wenzel-lab/flow-microscopy-platform/parts/optics/8.7-20mm-circular-lens.md

# 8.7° 20mm Circular Beam Optics

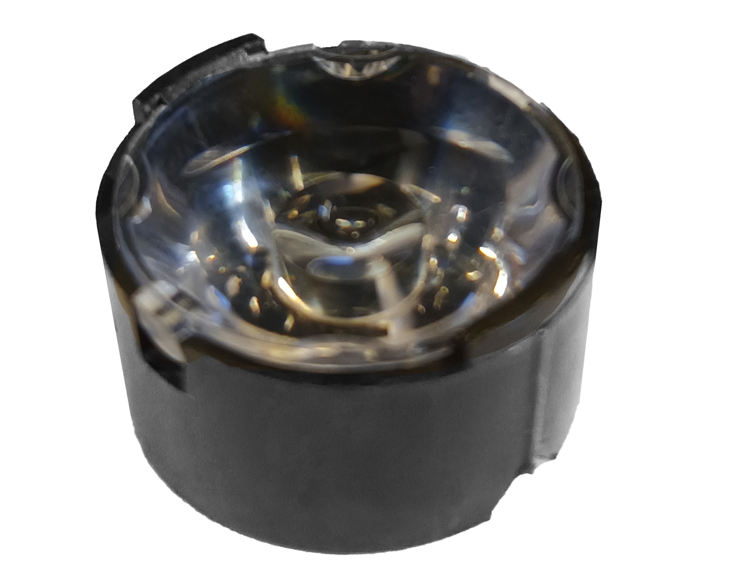
[picture p37: images/LED3.jpg]


_Suppliers:_ 

* [Luxeonstar / Lens](https://www.luxeonstar.com/carclo-8.7-degree-20mm-optic)

* [Luxeonstar / Holder](https://www.luxeonstar.com/carclo-20mm-round-optic-holder-black)
