wenzel-lab/flow-microscopy-platform/resin-legs.md

# Resin filled legs

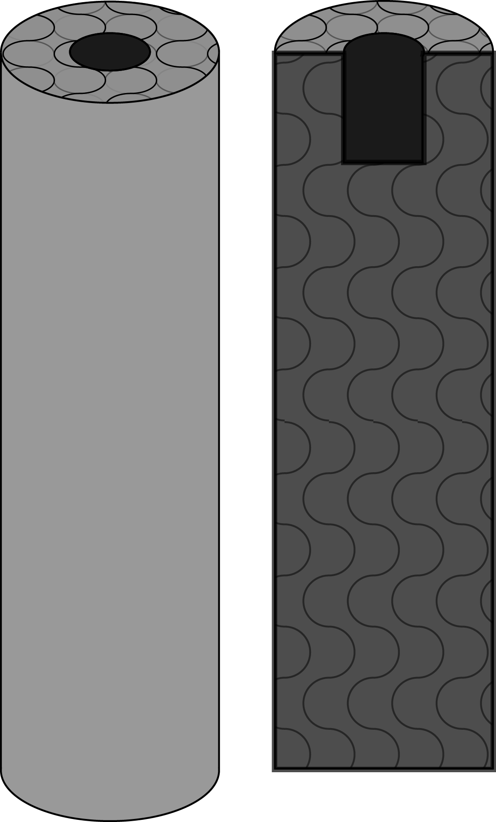
[picture p52: images/patas.jpg]


###What are they?

They are...

###How do we make them?

First...

>i **Please Note:** 
>i This site is under construction.
