wenzel-lab/flow-microscopy-platform/images/2-levels.jpg

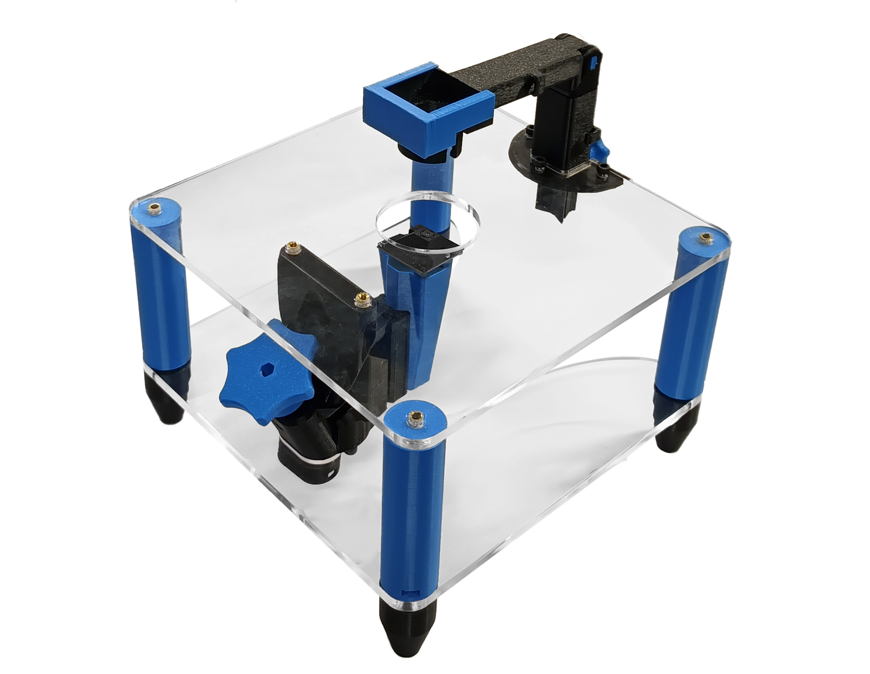
images/2-levels.jpg
