wenzel-lab/flow-microscopy-platform/images/2pin-du-pont-connector.png

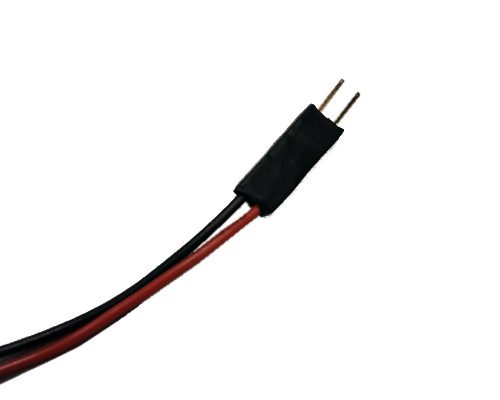
images/2pin-du-pont-connector.png
