wenzel-lab/flow-microscopy-platform/images/3-level-station.jpg

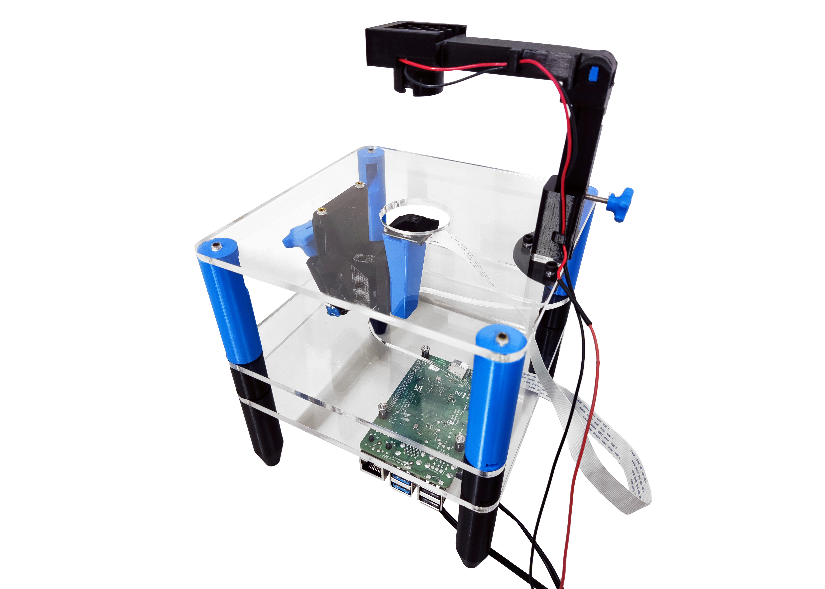
images/3-level-station.jpg
