wenzel-lab/flow-microscopy-platform/images/arm-slider.png

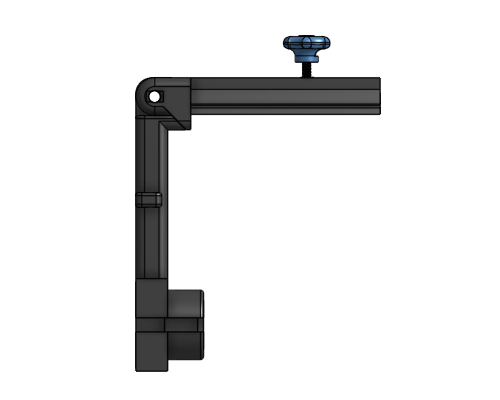
images/arm-slider.png
