wenzel-lab/flow-microscopy-platform/images/arm-slider_1.png

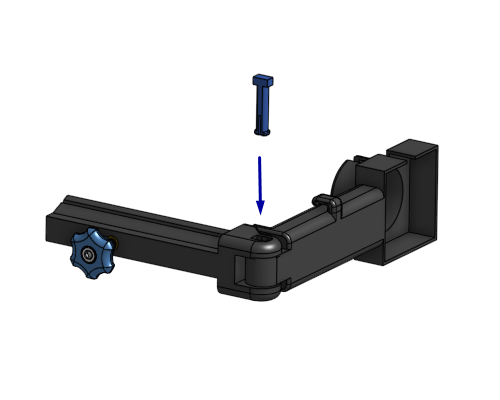
images/arm-slider_1.png
