wenzel-lab/flow-microscopy-platform/images/arm-slider_2.png

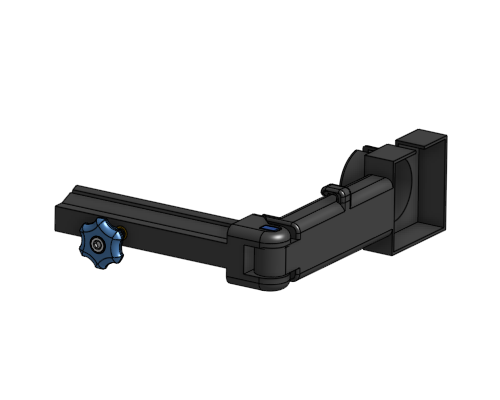
images/arm-slider_2.png
