wenzel-lab/flow-microscopy-platform/images/BrimRemoval.png

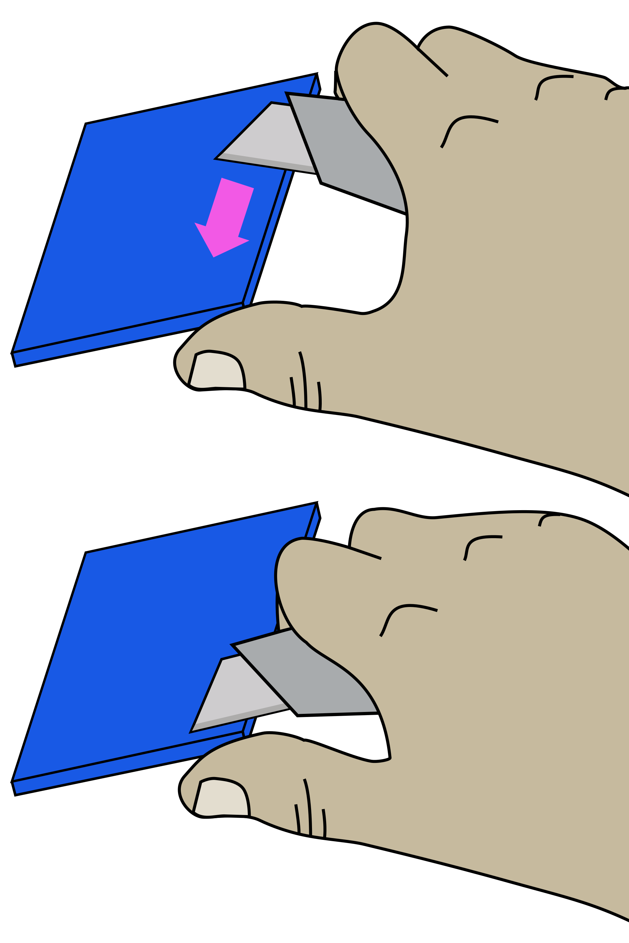
images/BrimRemoval.png
