wenzel-lab/flow-microscopy-platform/images/cable-clip.jpg

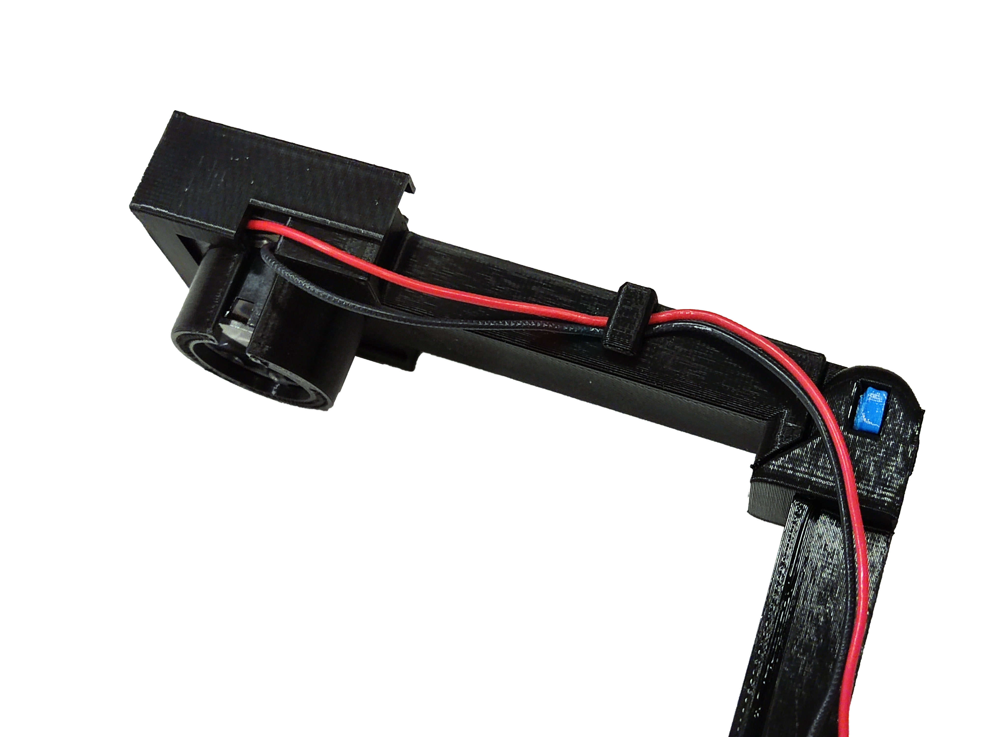
images/cable-clip.jpg
