wenzel-lab/flow-microscopy-platform/images/cable-clip_1.jpg

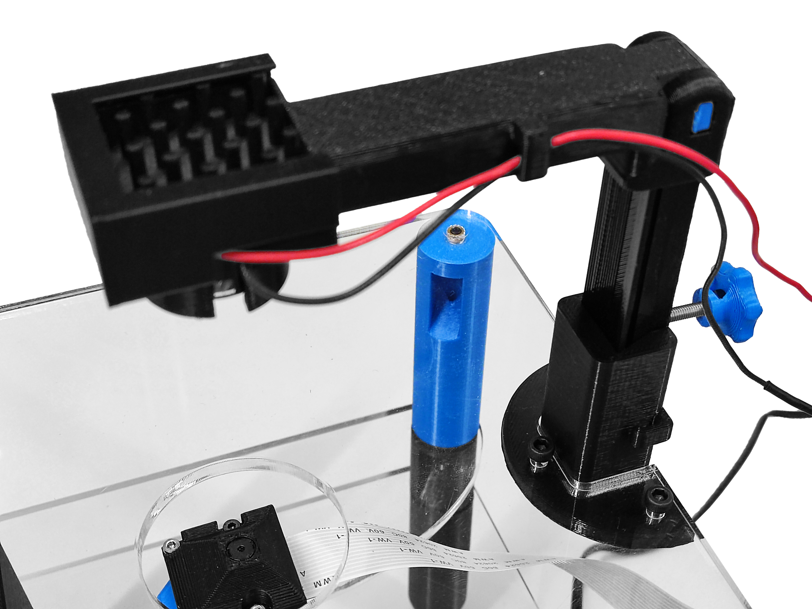
images/cable-clip_1.jpg
