wenzel-lab/flow-microscopy-platform/images/cable-clip_2.jpg

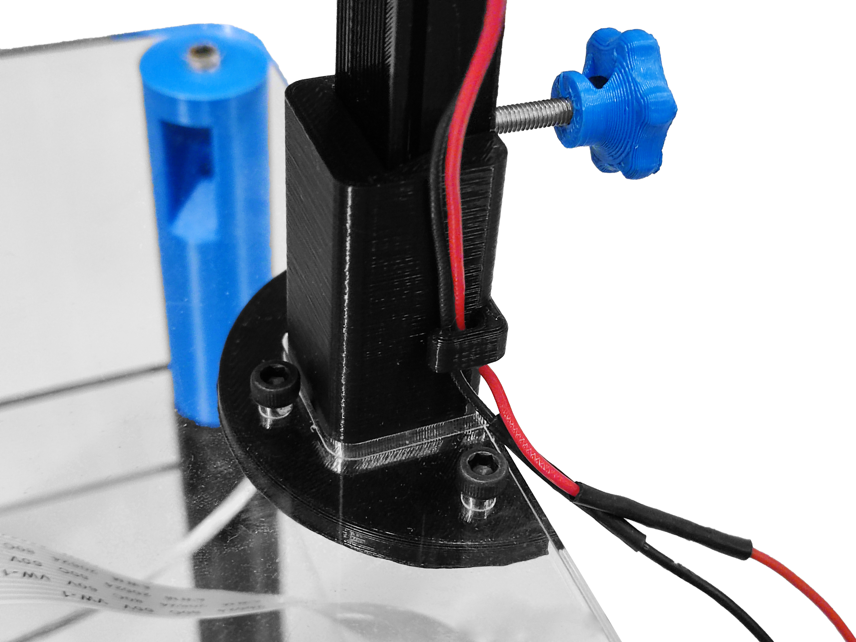
images/cable-clip_2.jpg
