wenzel-lab/flow-microscopy-platform/images/cable-clip_3.jpg

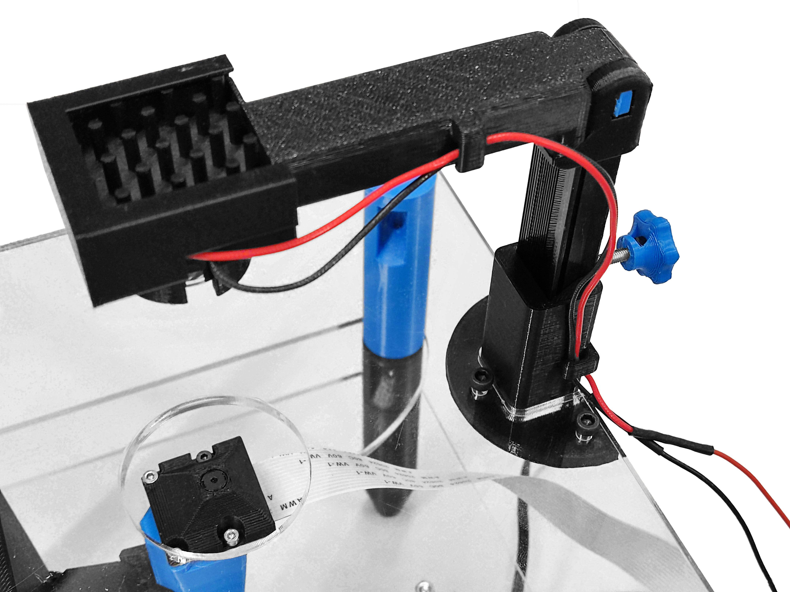
images/cable-clip_3.jpg
