wenzel-lab/flow-microscopy-platform/images/cap.jpg

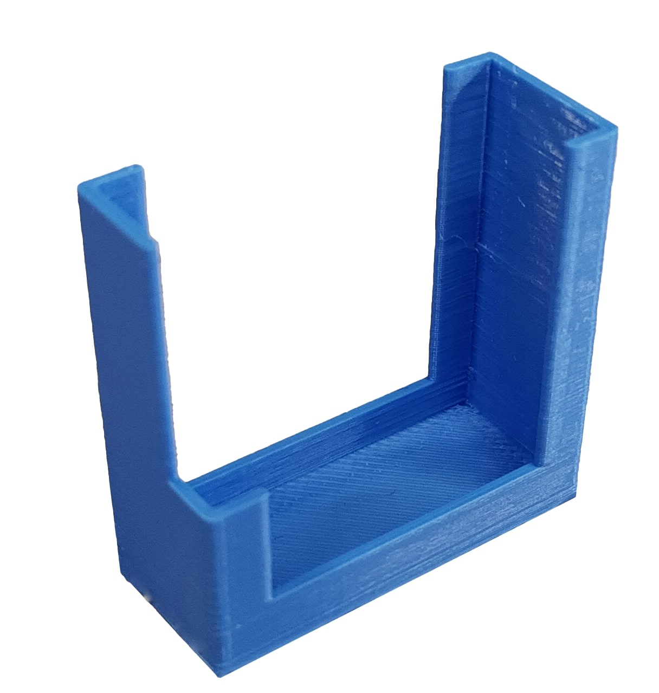
images/cap.jpg
