wenzel-lab/flow-microscopy-platform/images/DuPont-2PIN-Connector.jpg

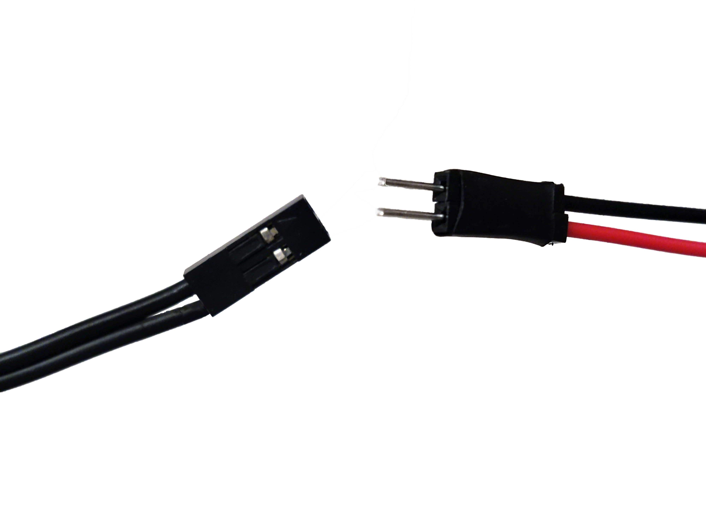
images/DuPont-2PIN-Connector.jpg
