wenzel-lab/flow-microscopy-platform/images/feet-M-attached.jpg

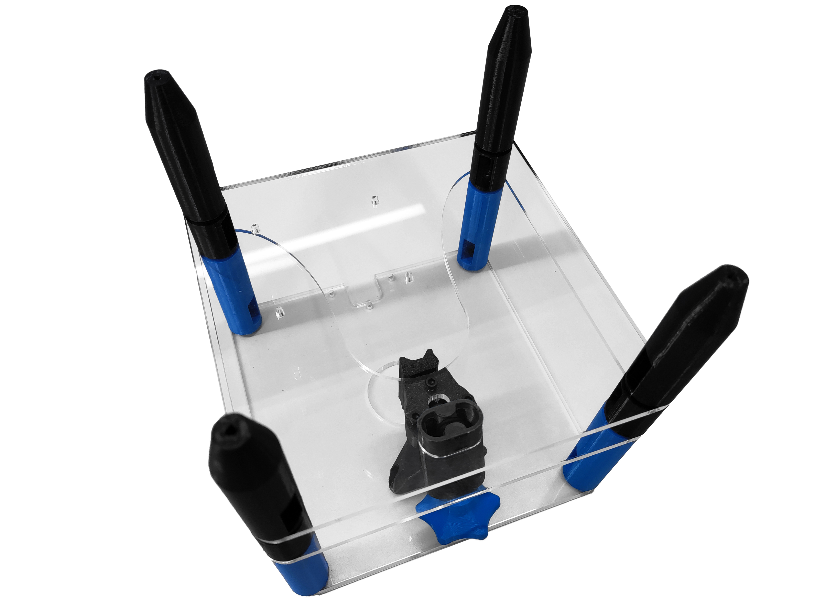
images/feet-M-attached.jpg
