wenzel-lab/flow-microscopy-platform/images/feet-M-attached_1.jpg

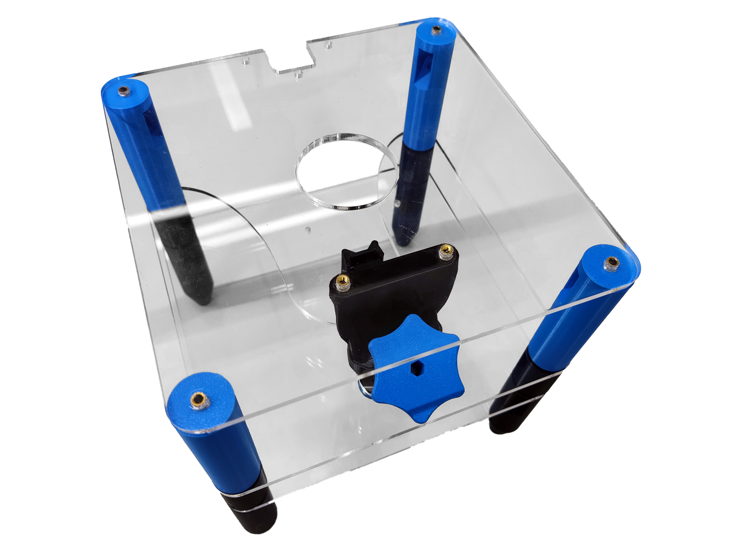
images/feet-M-attached_1.jpg
