wenzel-lab/flow-microscopy-platform/images/Female-crimp-pin.jpg

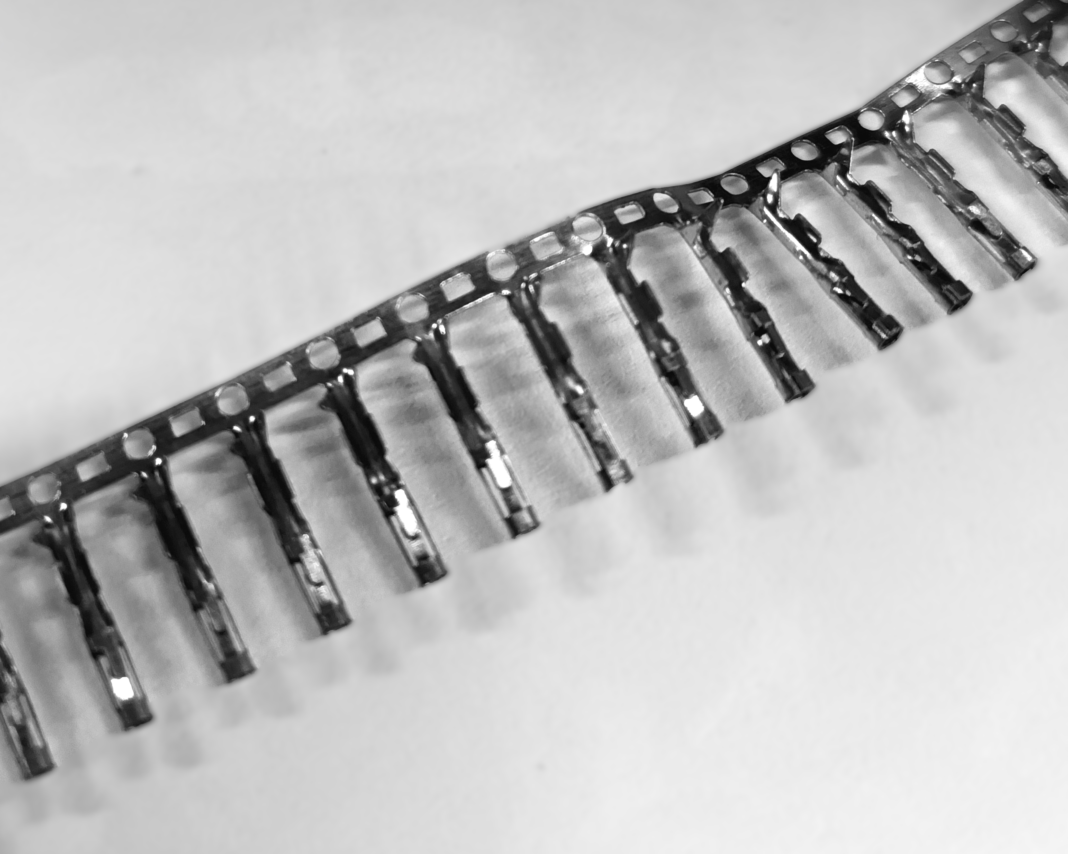
images/Female-crimp-pin.jpg
