wenzel-lab/flow-microscopy-platform/images/flow-platform.jpg

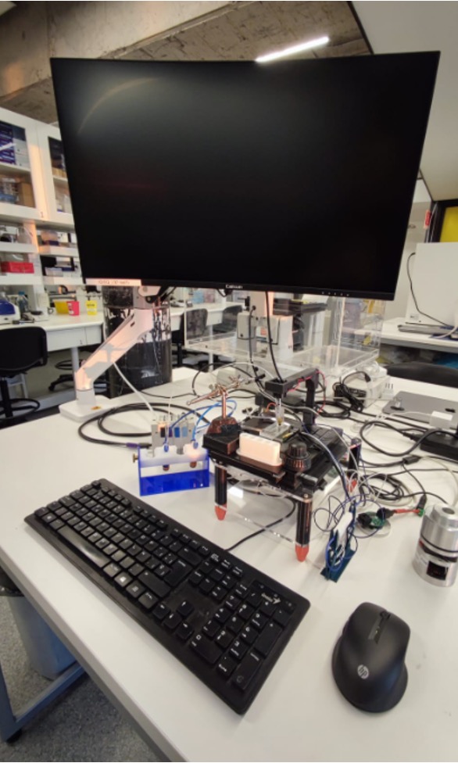
images/flow-platform.jpg
