wenzel-lab/flow-microscopy-platform/images/foot-M-attached.jpg

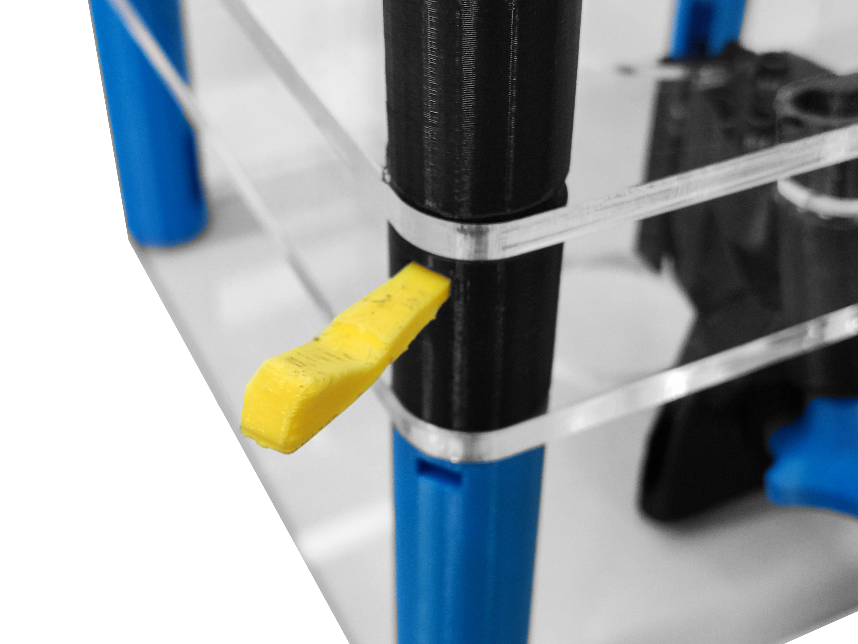
images/foot-M-attached.jpg
