wenzel-lab/flow-microscopy-platform/images/foot-M-attached_1.jpg

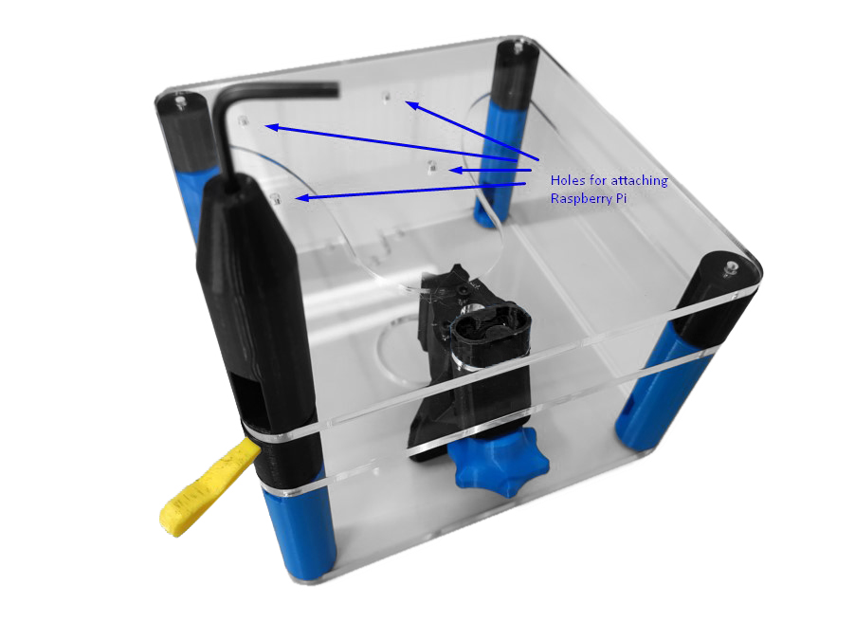
images/foot-M-attached_1.jpg
