wenzel-lab/flow-microscopy-platform/images/foot-M-attached_2.jpg

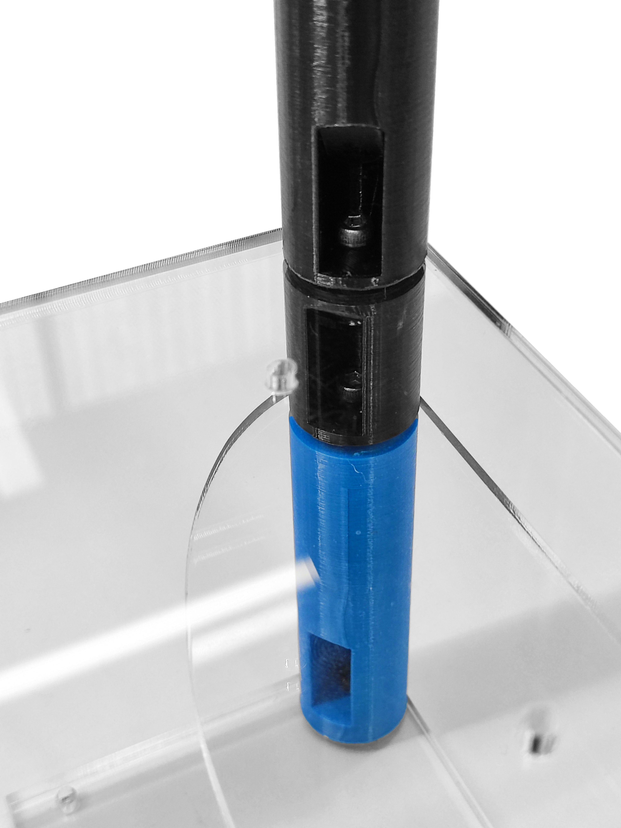
images/foot-M-attached_2.jpg
