wenzel-lab/flow-microscopy-platform/images/foot-M-attached_3.jpg

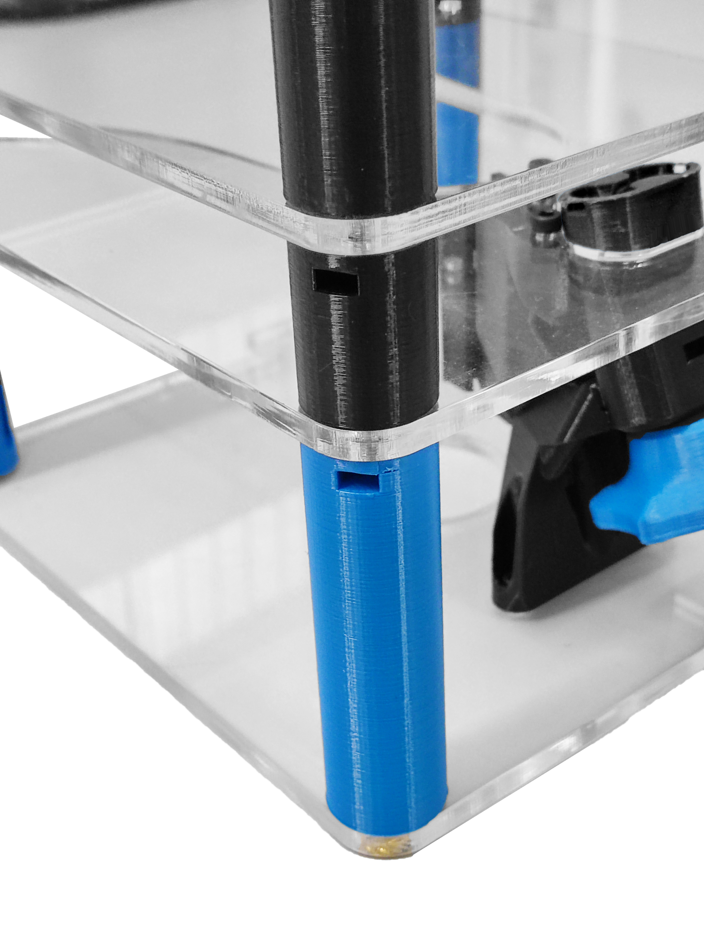
images/foot-M-attached_3.jpg
