wenzel-lab/flow-microscopy-platform/images/foot-M.jpg

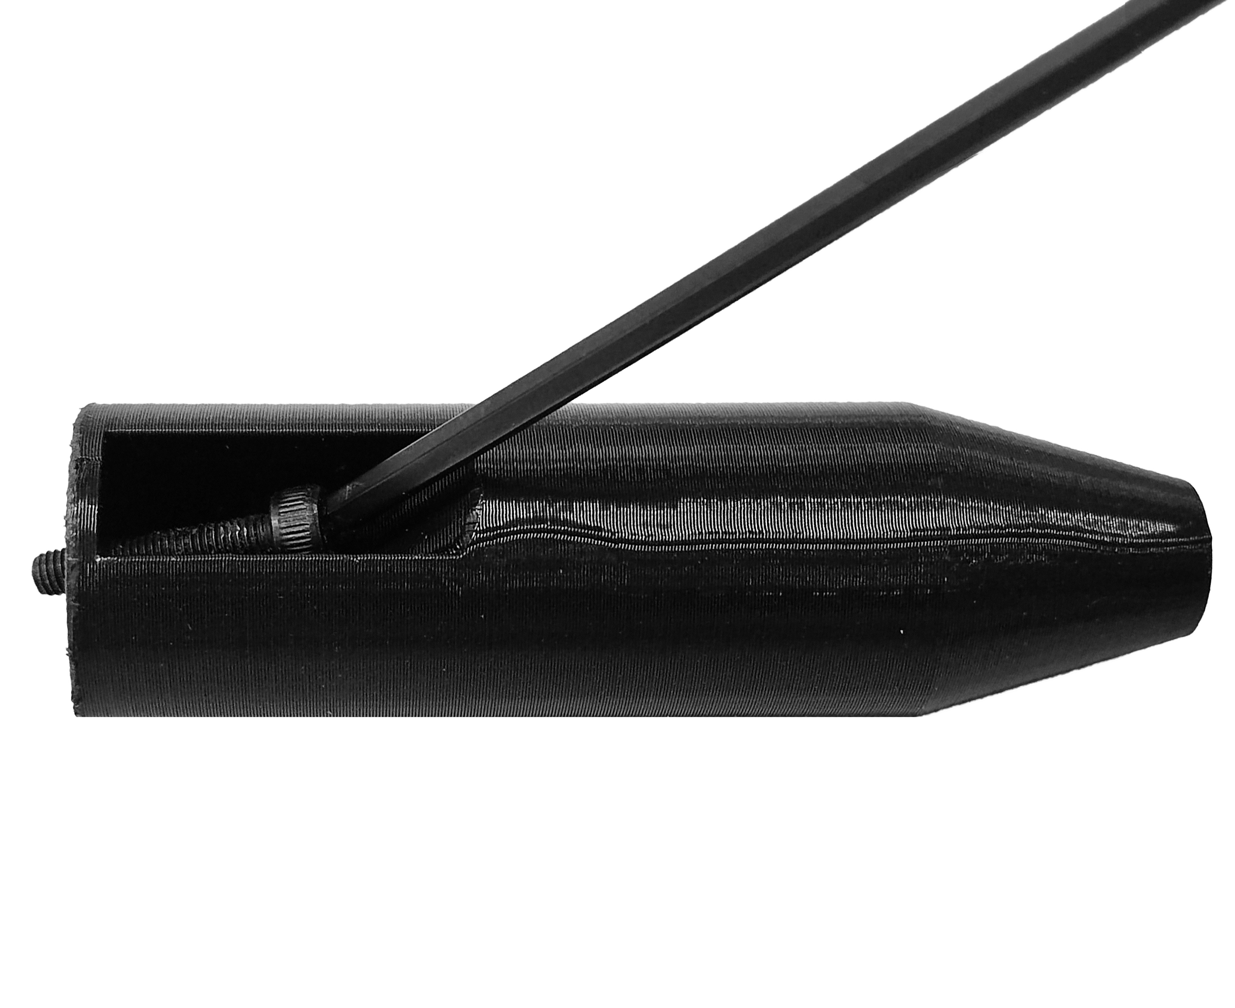
images/foot-M.jpg
