wenzel-lab/flow-microscopy-platform/images/heat-insert_top-plate.png

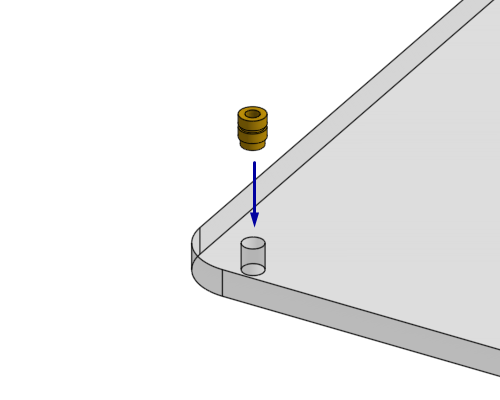
images/heat-insert_top-plate.png
