wenzel-lab/flow-microscopy-platform/images/heat-insert_top-plate_1.png

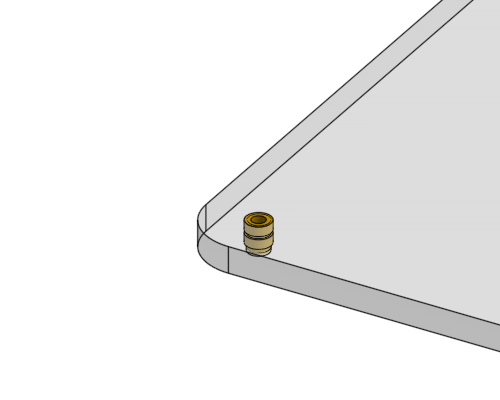
images/heat-insert_top-plate_1.png
