wenzel-lab/flow-microscopy-platform/images/heat-insert_top-plate_2.png

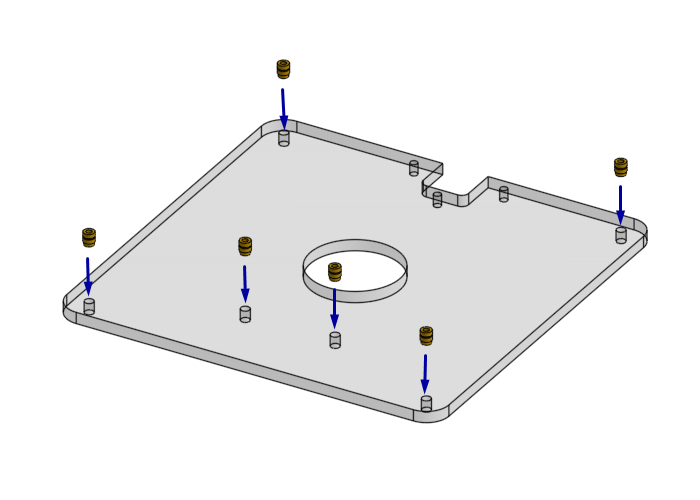
images/heat-insert_top-plate_2.png
