wenzel-lab/flow-microscopy-platform/images/heat-insert_top-plate_3.png

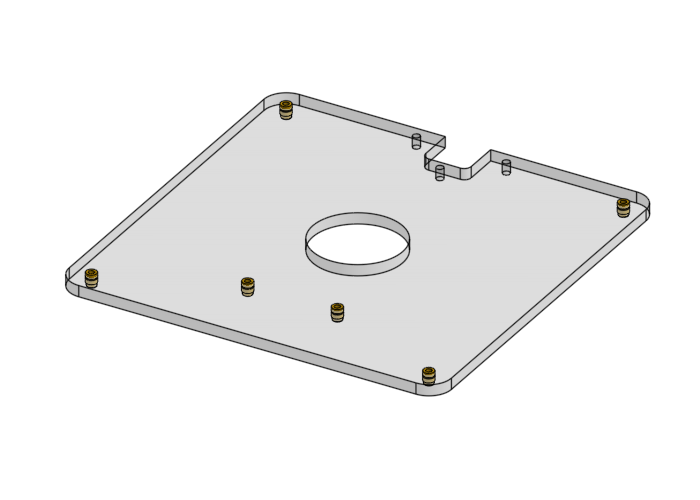
images/heat-insert_top-plate_3.png
