wenzel-lab/flow-microscopy-platform/images/iii.jpg

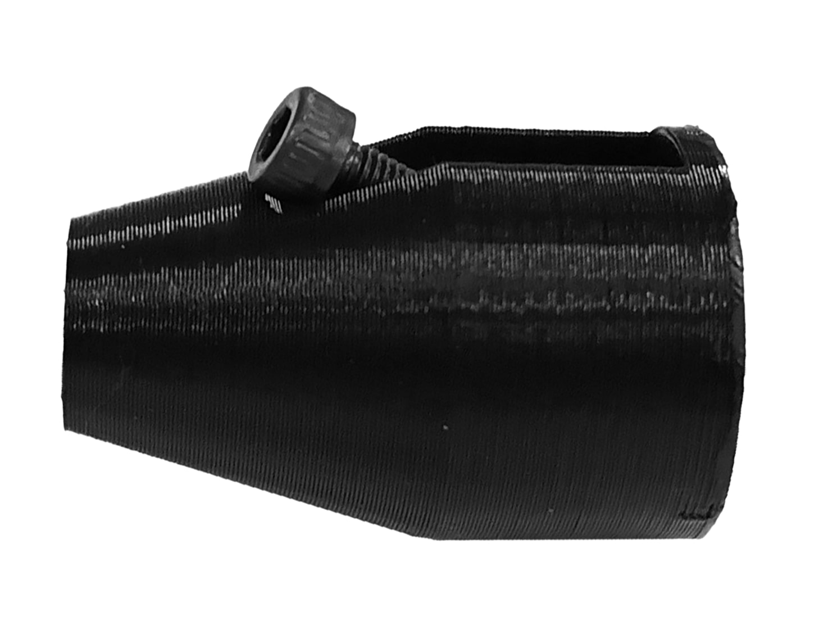
images/iii.jpg
