wenzel-lab/flow-microscopy-platform/images/LED1.jpg

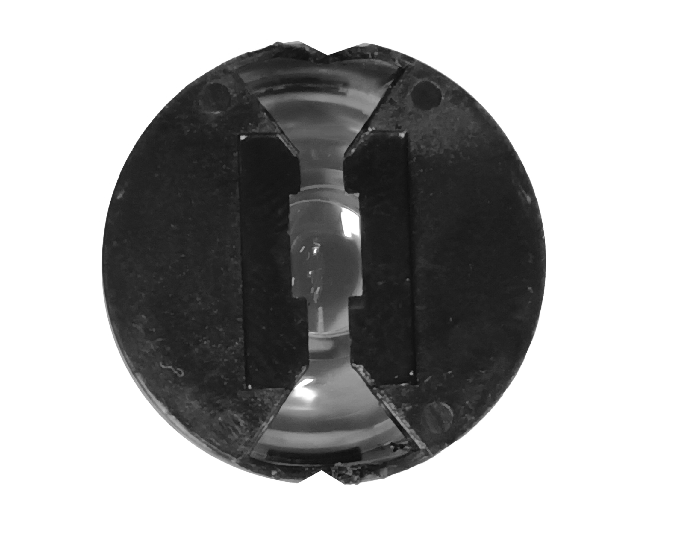
images/LED1.jpg
