wenzel-lab/flow-microscopy-platform/images/LED4.jpg

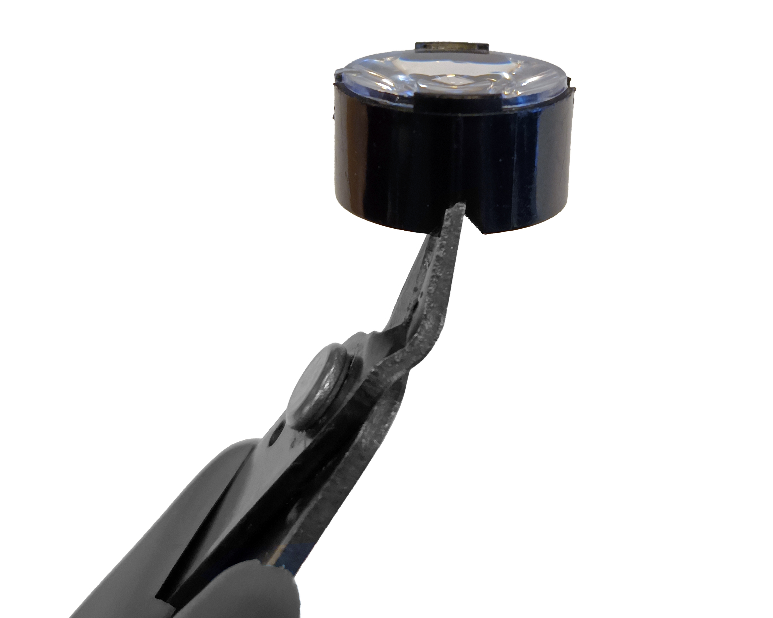
images/LED4.jpg
