wenzel-lab/flow-microscopy-platform/images/led-lens-sink.png

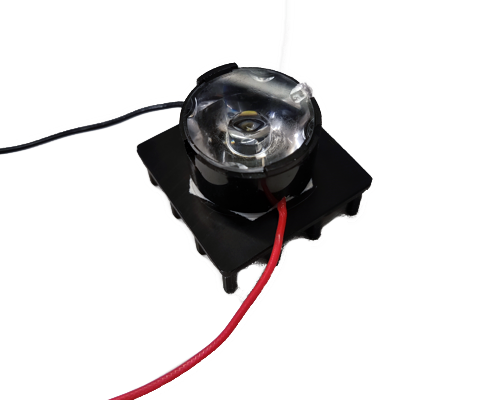
images/led-lens-sink.png
