wenzel-lab/flow-microscopy-platform/images/LED.jpg

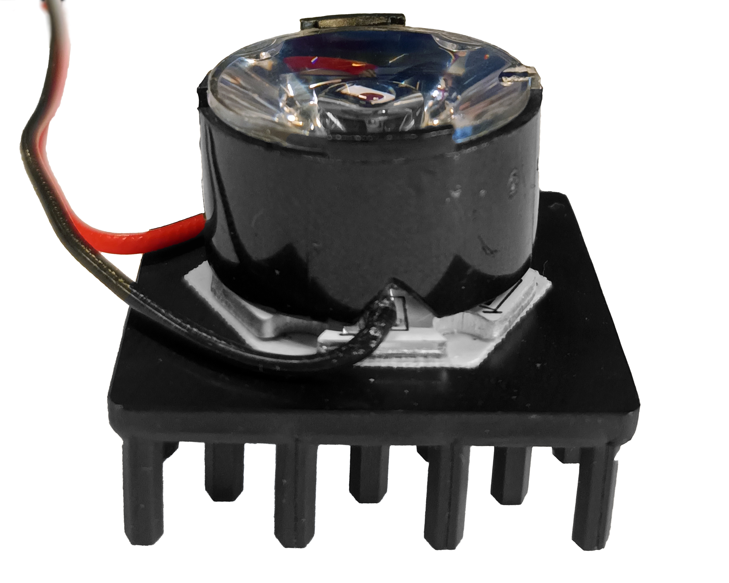
images/LED.jpg
