wenzel-lab/flow-microscopy-platform/images/lens-holder-1.png

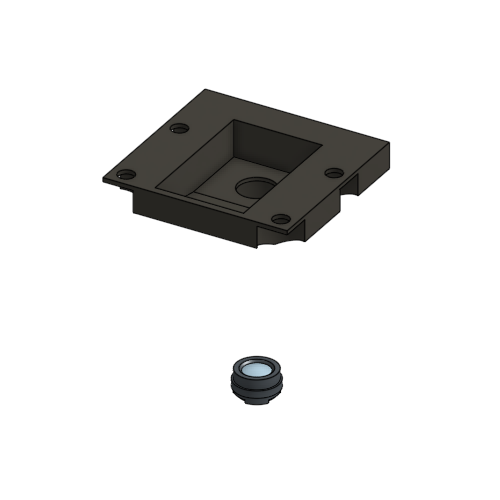
images/lens-holder-1.png
