wenzel-lab/flow-microscopy-platform/images/lens-holder-2.png

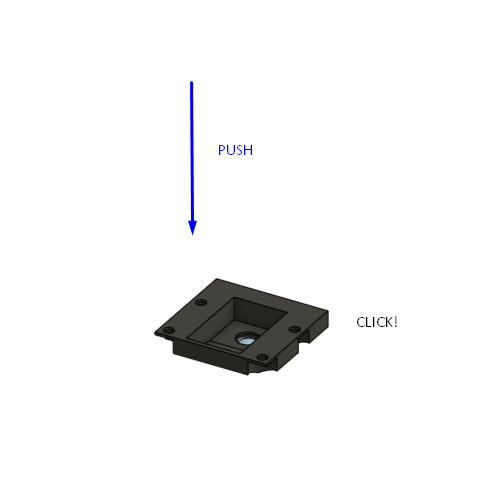
images/lens-holder-2.png
