wenzel-lab/flow-microscopy-platform/images/lens-holder-3.png

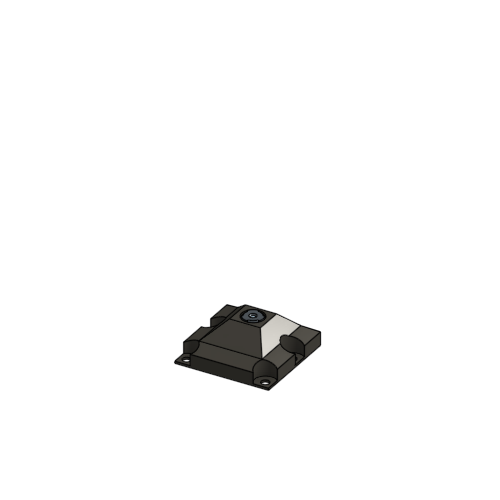
images/lens-holder-3.png
