wenzel-lab/flow-microscopy-platform/images/LH-Hinsert.jpg

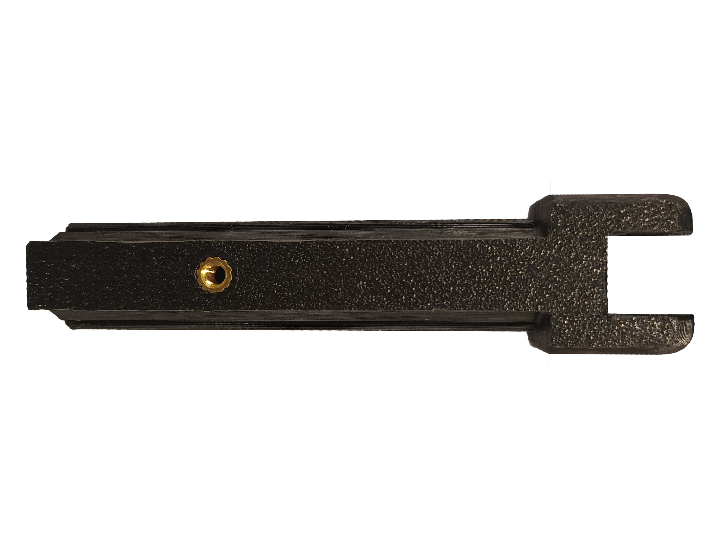
images/LH-Hinsert.jpg
