wenzel-lab/flow-microscopy-platform/images/LH-knob.jpg

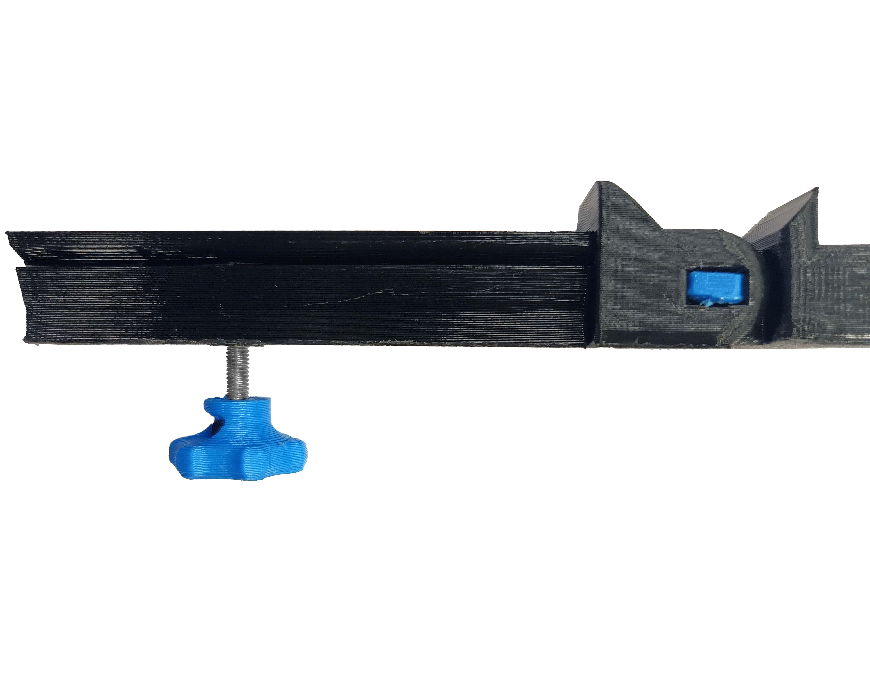
images/LH-knob.jpg
