wenzel-lab/flow-microscopy-platform/images/LH-pin.jpg

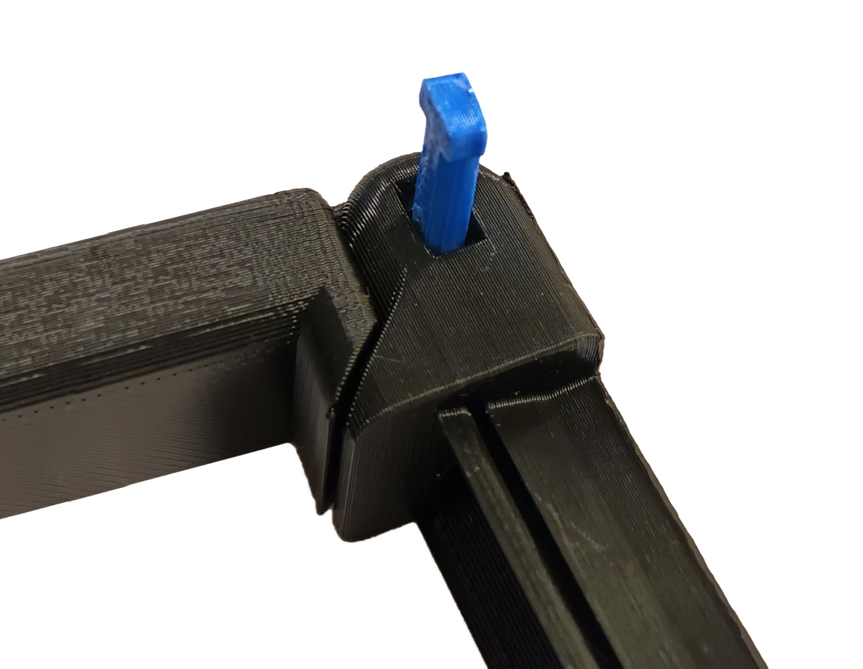
images/LH-pin.jpg
