wenzel-lab/flow-microscopy-platform/images/middle_plate_to_focus.jpg

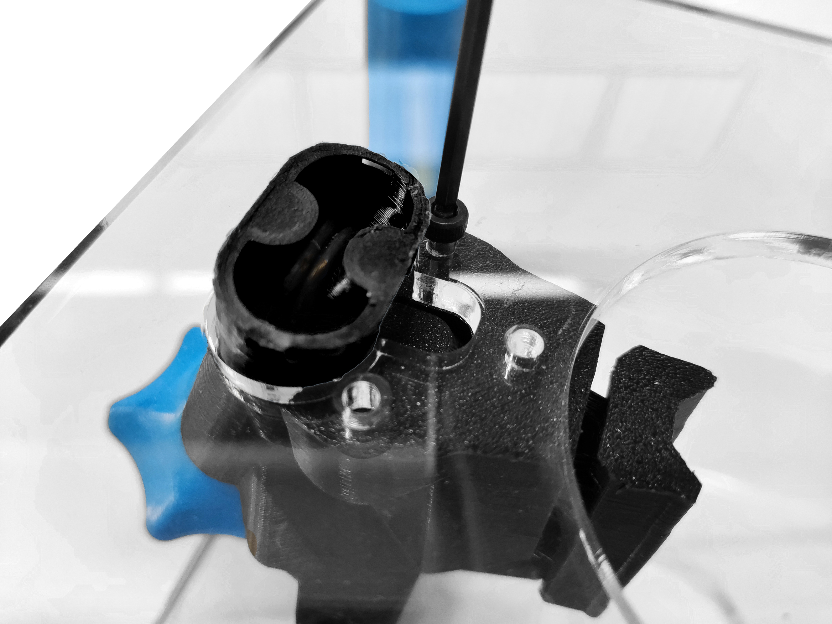
images/middle_plate_to_focus.jpg
