wenzel-lab/flow-microscopy-platform/images/mount-screw-1.png

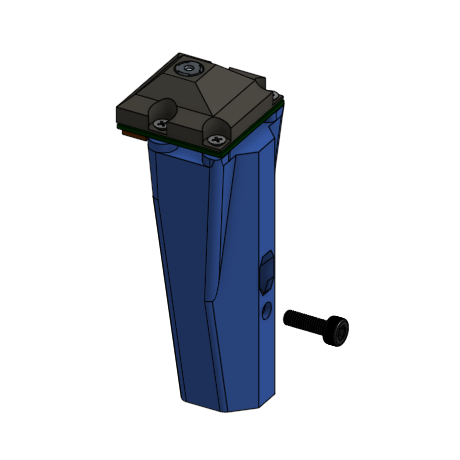
images/mount-screw-1.png
