wenzel-lab/flow-microscopy-platform/images/mount-screw.png

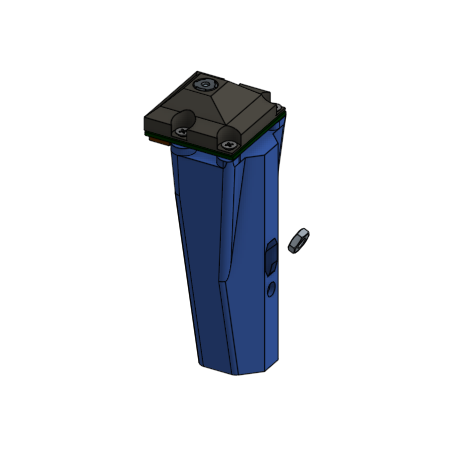
images/mount-screw.png
