wenzel-lab/flow-microscopy-platform/images/mount_base.png

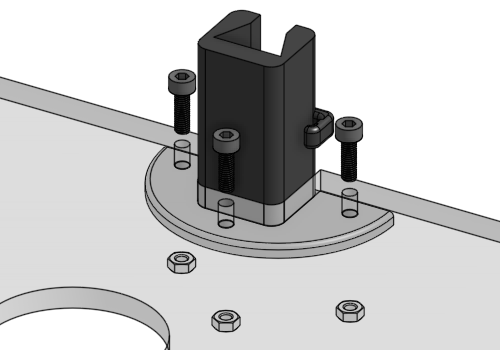
images/mount_base.png
