wenzel-lab/flow-microscopy-platform/images/mount_base_1.png

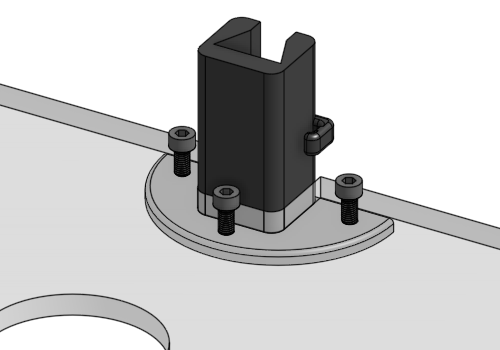
images/mount_base_1.png
