wenzel-lab/flow-microscopy-platform/images/mount_base_2.png

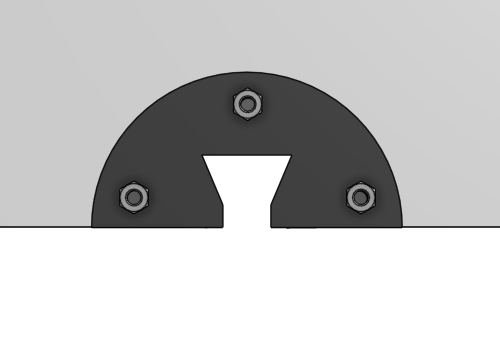
images/mount_base_2.png
