wenzel-lab/flow-microscopy-platform/images/mount_boards_3.jpg

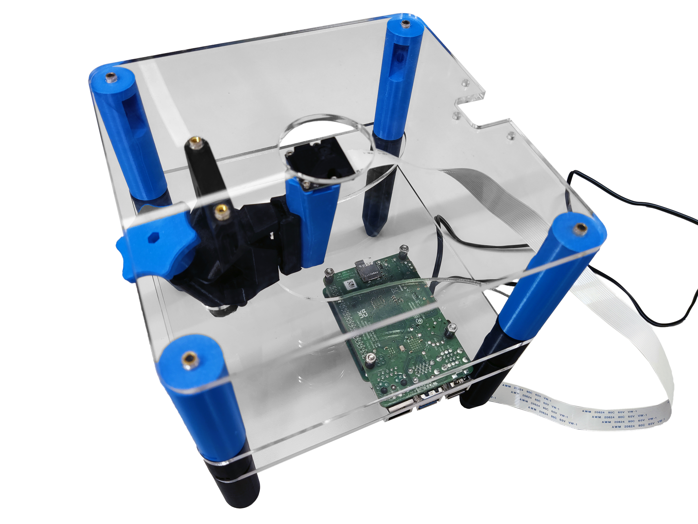
images/mount_boards_3.jpg
