wenzel-lab/flow-microscopy-platform/images/mount_optics.jpg

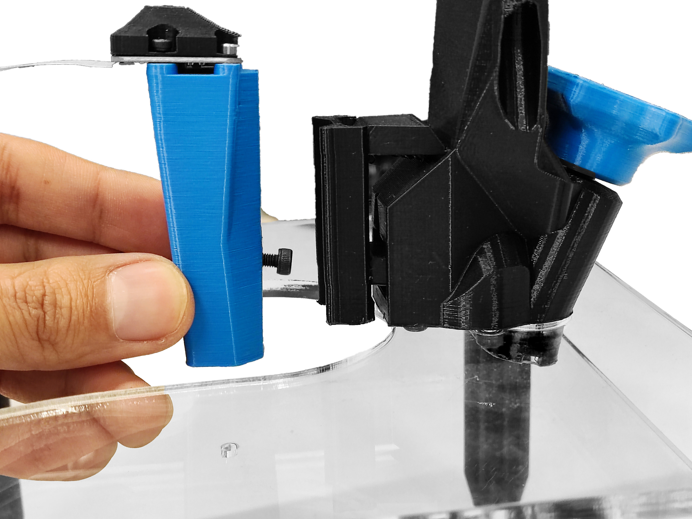
images/mount_optics.jpg
