wenzel-lab/flow-microscopy-platform/images/mount_optics_1.jpg

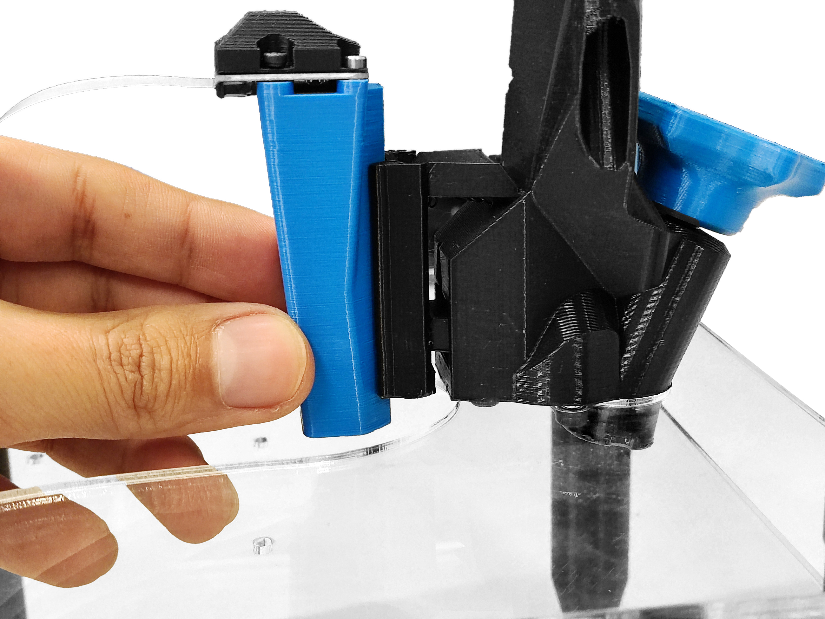
images/mount_optics_1.jpg
