wenzel-lab/flow-microscopy-platform/images/mount_spacers.jpg

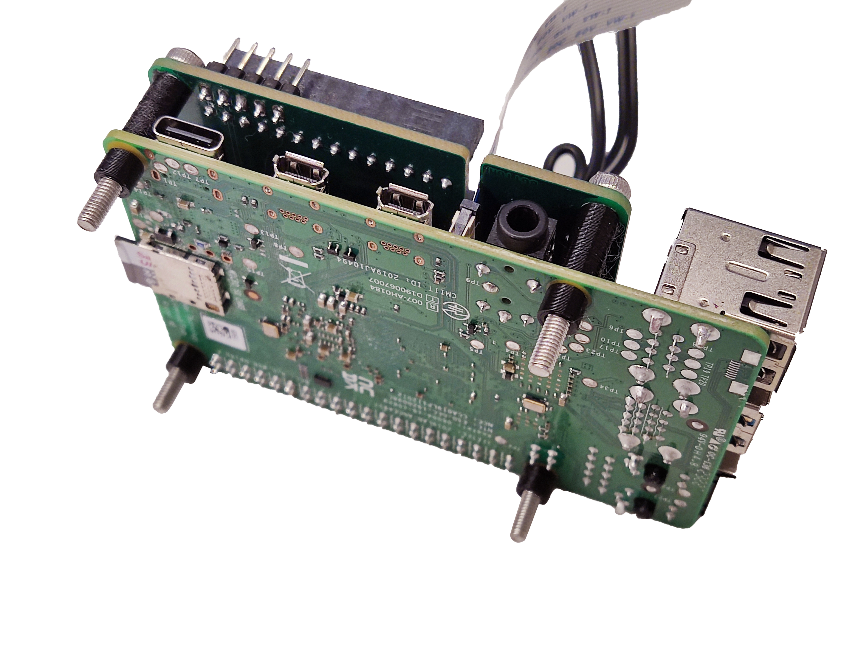
images/mount_spacers.jpg
