wenzel-lab/flow-microscopy-platform/images/nutpushers.jpg

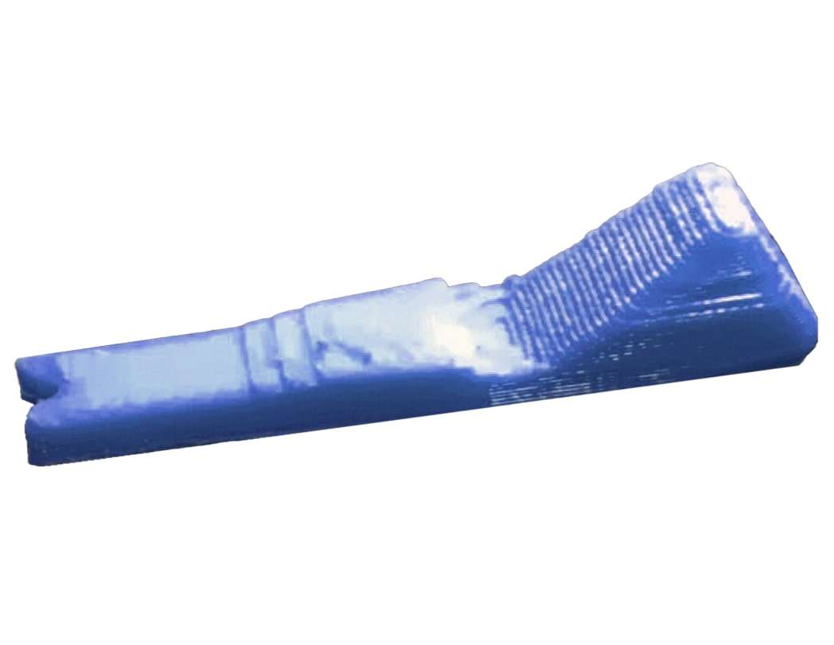
images/nutpushers.jpg
