wenzel-lab/flow-microscopy-platform/images/partelight.jpg

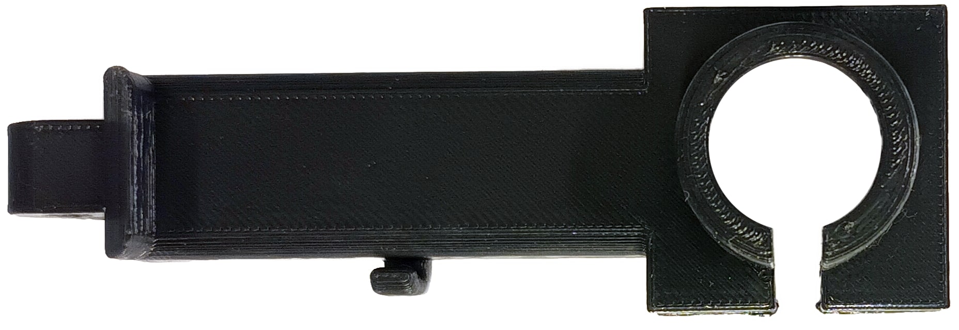
images/partelight.jpg
