wenzel-lab/flow-microscopy-platform/images/partelighthold.jpg

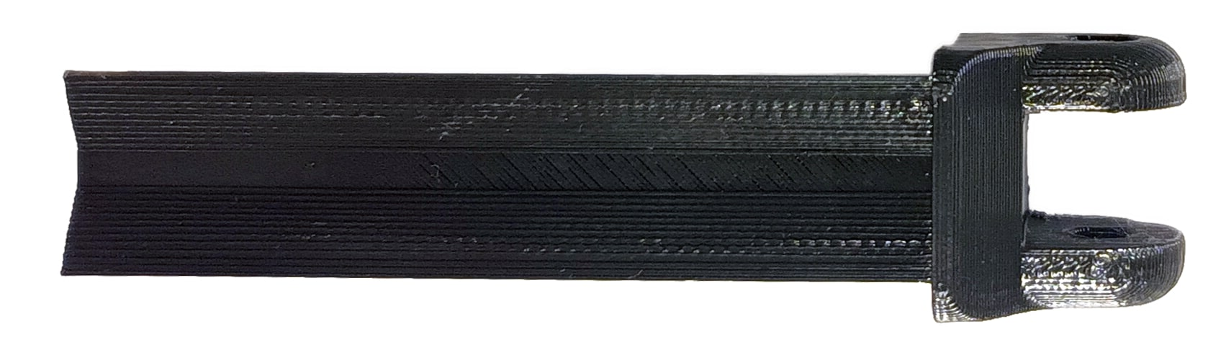
images/partelighthold.jpg
