wenzel-lab/flow-microscopy-platform/images/partelightholder.jpg

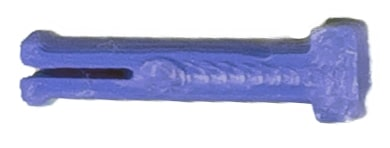
images/partelightholder.jpg
