wenzel-lab/flow-microscopy-platform/images/Pi-Hat_StrobeModule.jpg

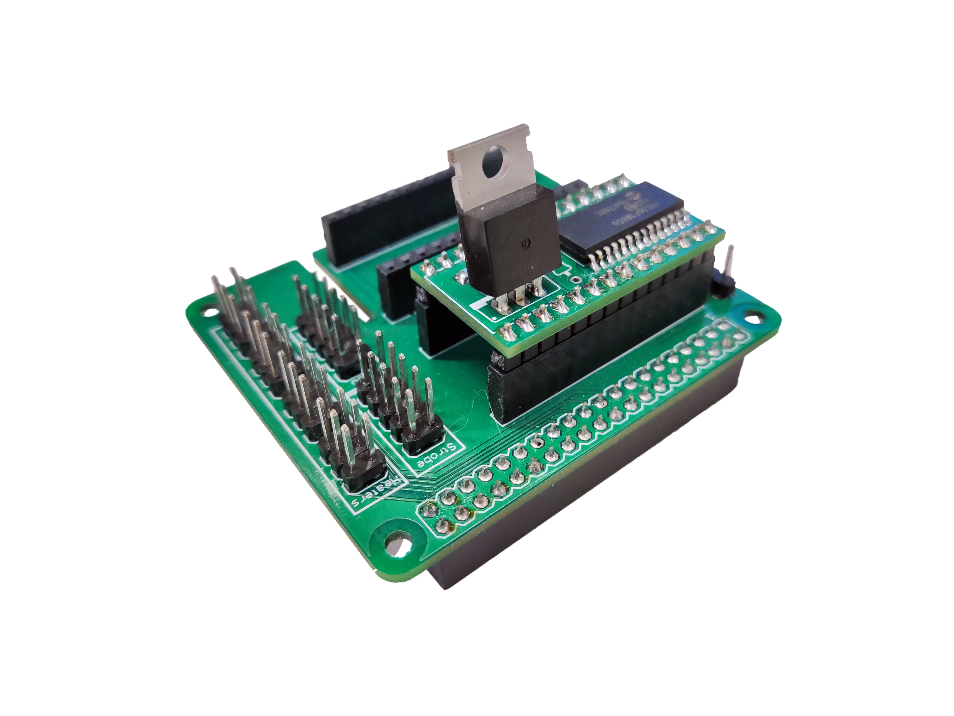
images/Pi-Hat_StrobeModule.jpg
