wenzel-lab/flow-microscopy-platform/images/picam1.png

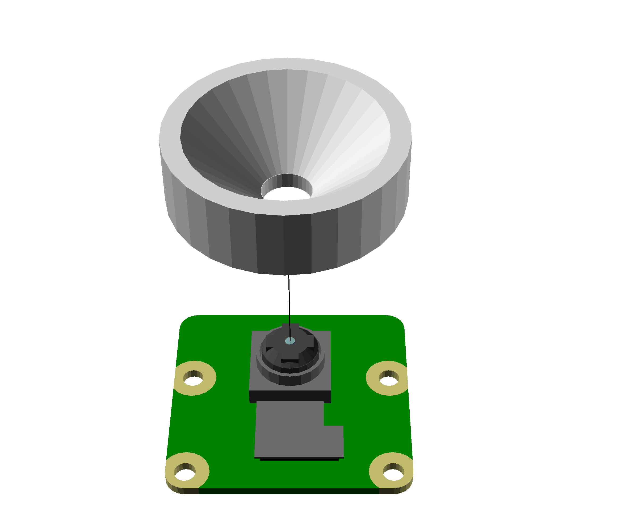
images/picam1.png
