wenzel-lab/flow-microscopy-platform/images/picam2.png

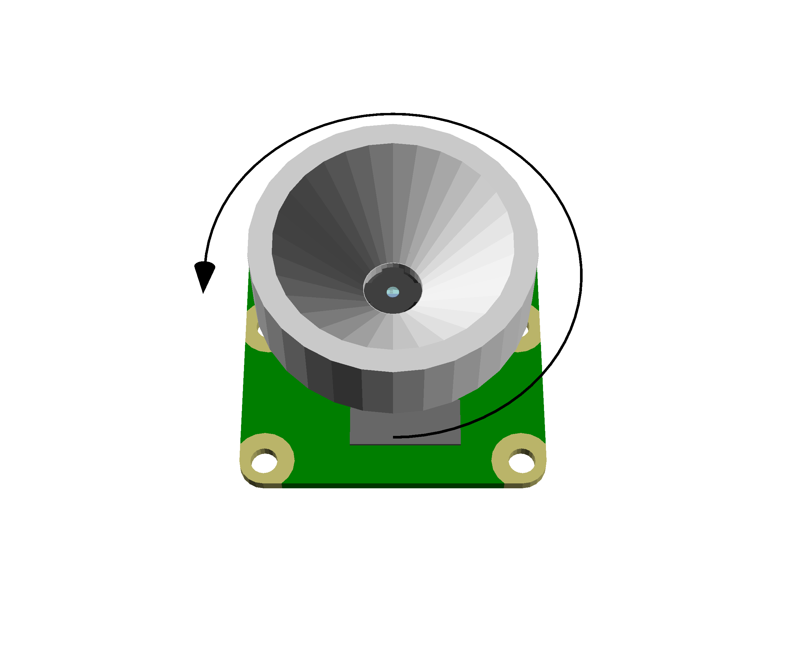
images/picam2.png
