wenzel-lab/flow-microscopy-platform/images/picam3.png

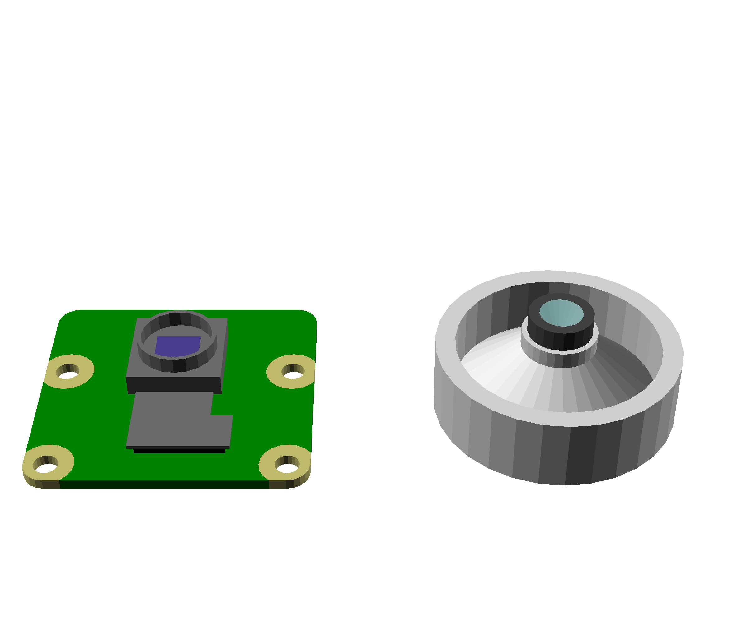
images/picam3.png
