wenzel-lab/flow-microscopy-platform/images/prepare-electronics.jpg

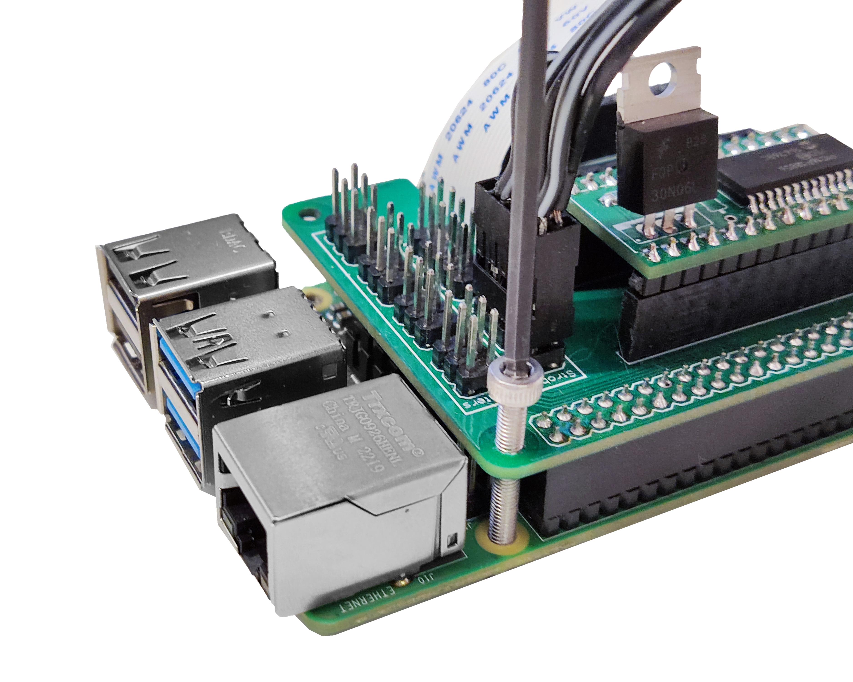
images/prepare-electronics.jpg
