wenzel-lab/flow-microscopy-platform/images/prepare-electronics_1.jpg

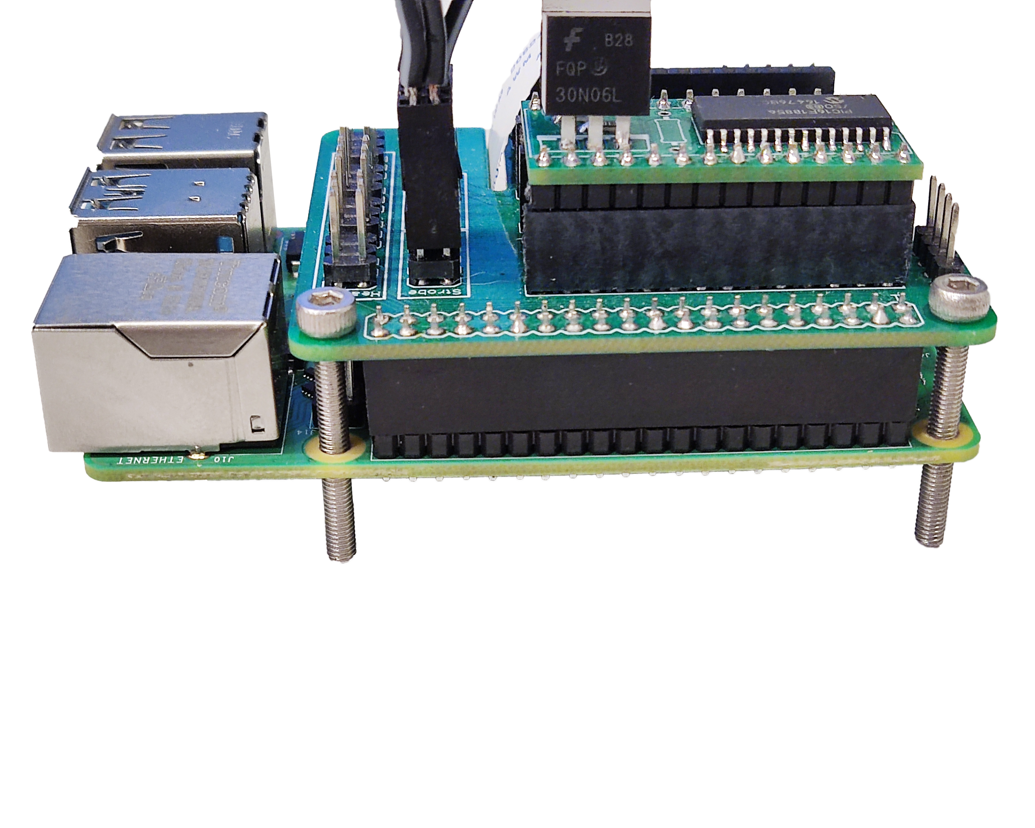
images/prepare-electronics_1.jpg
