wenzel-lab/flow-microscopy-platform/images/prepare-electronics_3.jpg

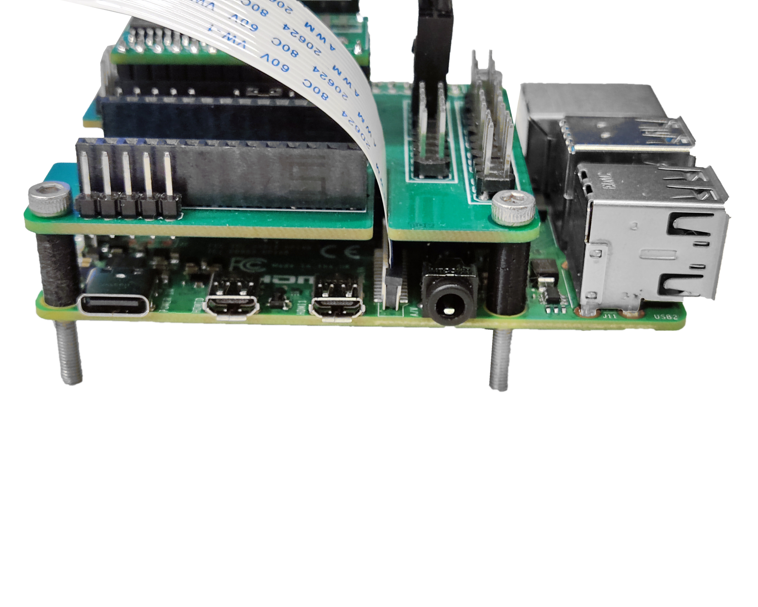
images/prepare-electronics_3.jpg
