wenzel-lab/flow-microscopy-platform/images/RPi_Pi-Hat_StrobeCable.jpg

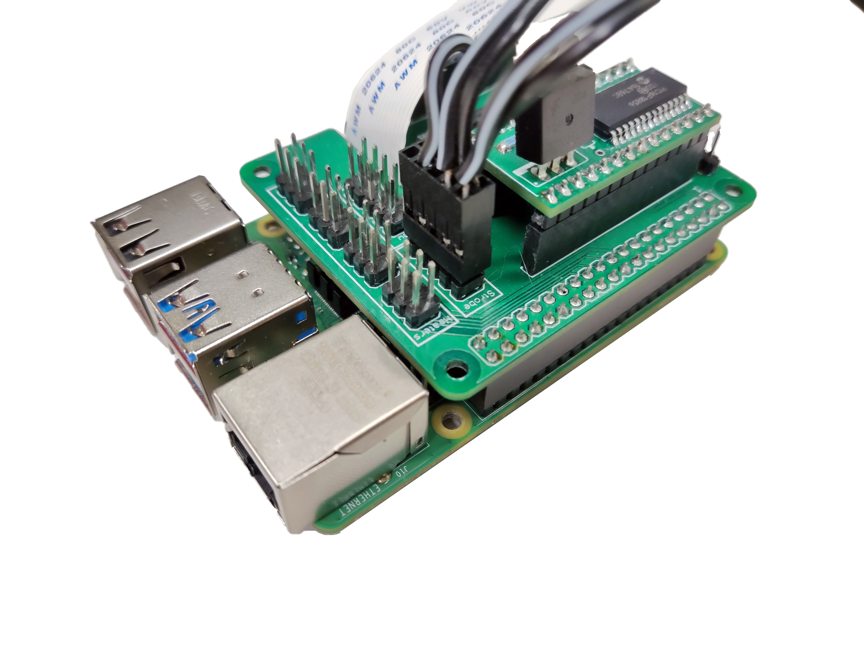
images/RPi_Pi-Hat_StrobeCable.jpg
