wenzel-lab/flow-microscopy-platform/images/RPi_RibbonCable.jpg

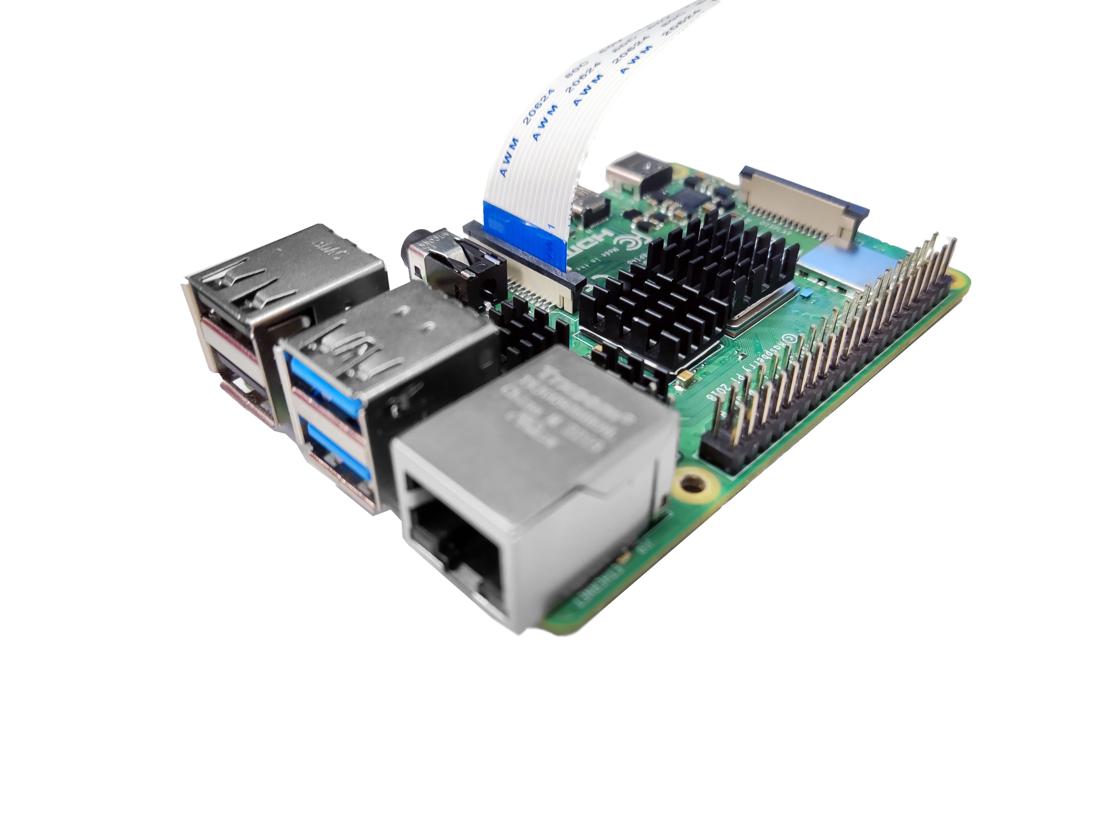
images/RPi_RibbonCable.jpg
