wenzel-lab/flow-microscopy-platform/images/screen.jpg

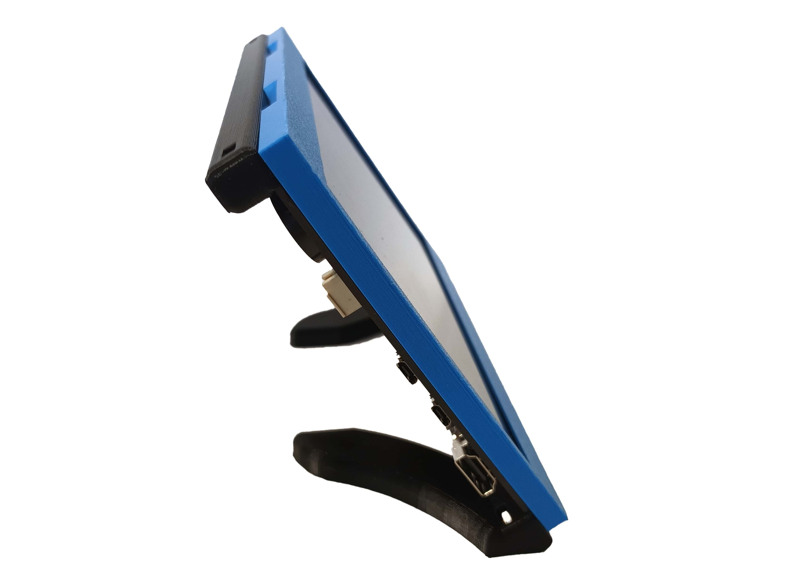
images/screen.jpg
