wenzel-lab/flow-microscopy-platform/images/screens.jpg

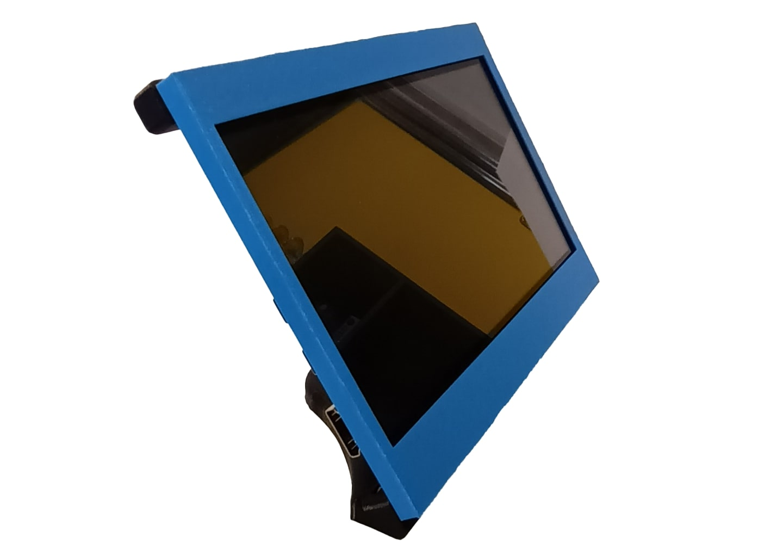
images/screens.jpg
