wenzel-lab/flow-microscopy-platform/images/silde-knob.jpg

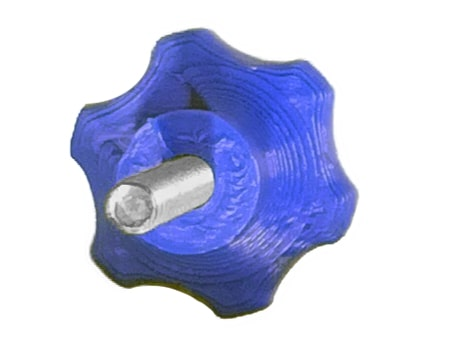
images/silde-knob.jpg
