wenzel-lab/flow-microscopy-platform/images/slider-insert.png

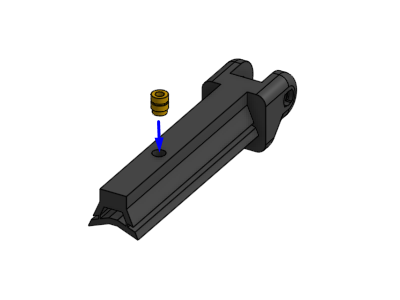
images/slider-insert.png
