wenzel-lab/flow-microscopy-platform/images/spacer-top-flip.jpg

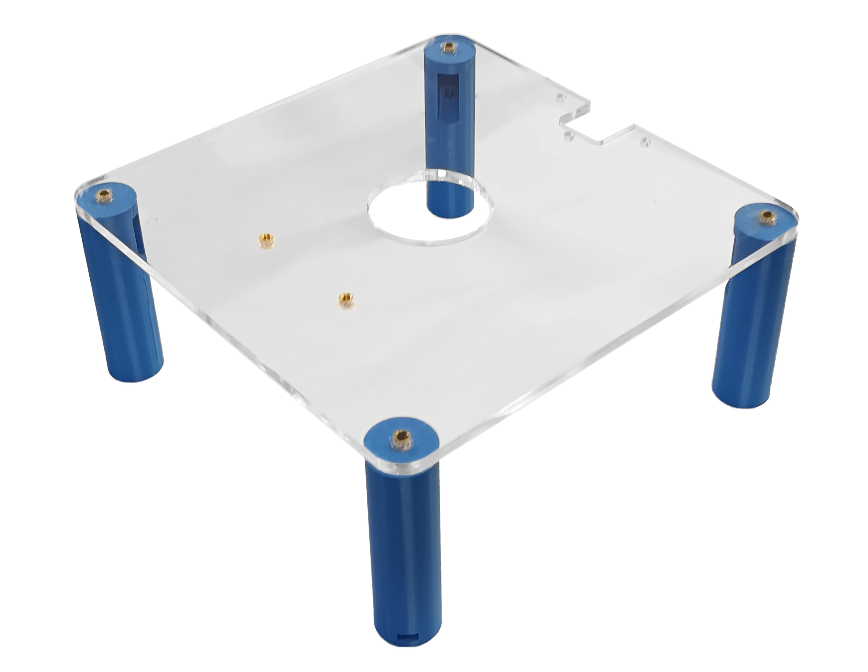
images/spacer-top-flip.jpg
