wenzel-lab/flow-microscopy-platform/images/spacer_screw_insertion_1.png

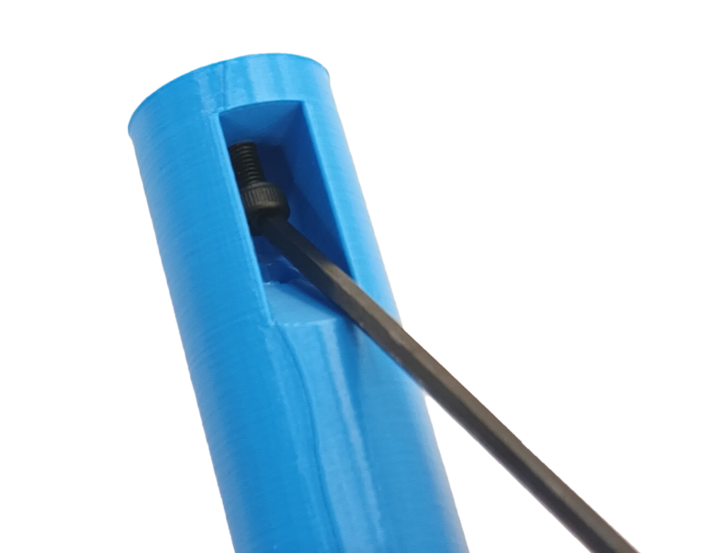
images/spacer_screw_insertion_1.png
