wenzel-lab/flow-microscopy-platform/images/spacer_screw_insertion_2.png

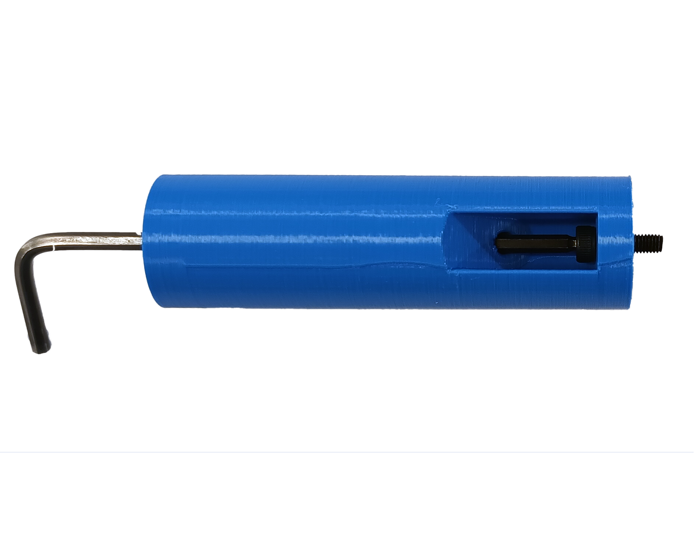
images/spacer_screw_insertion_2.png
