wenzel-lab/flow-microscopy-platform/images/spacer_top_attached.png

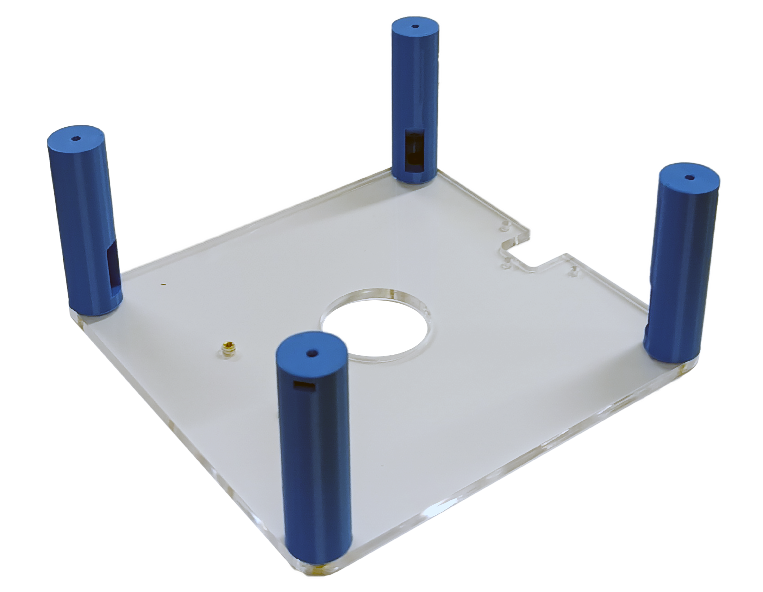
images/spacer_top_attached.png
