wenzel-lab/flow-microscopy-platform/images/standoff-M-attached-1.jpg

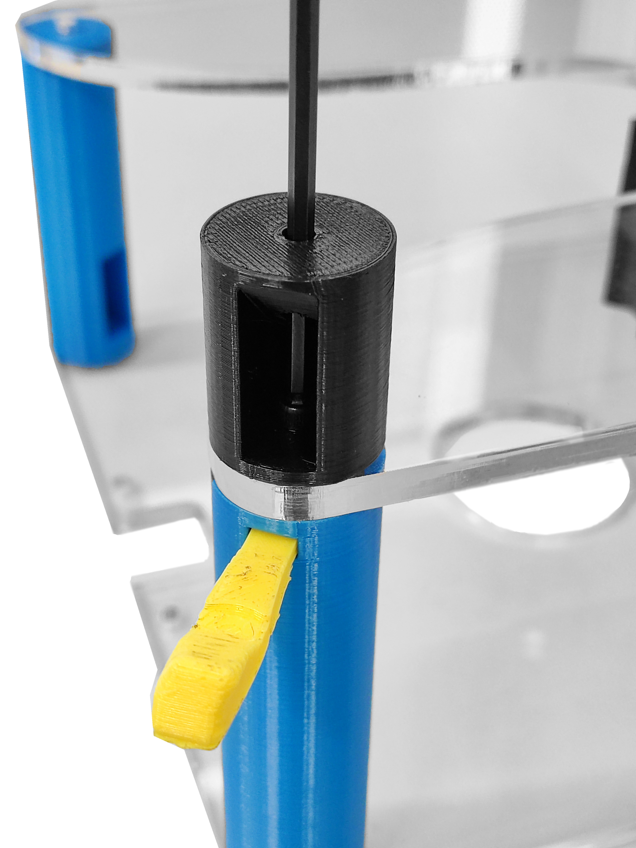
images/standoff-M-attached-1.jpg
