wenzel-lab/flow-microscopy-platform/images/standoff-M-attached-2.jpg

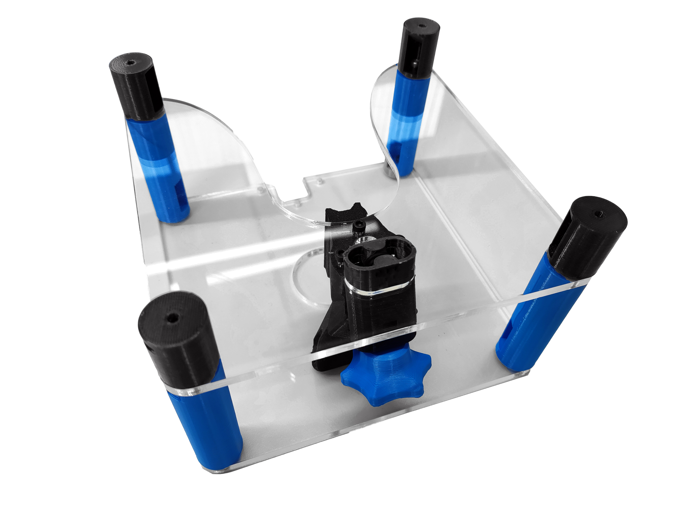
images/standoff-M-attached-2.jpg
