wenzel-lab/flow-microscopy-platform/images/standoff-M-attached.jpg

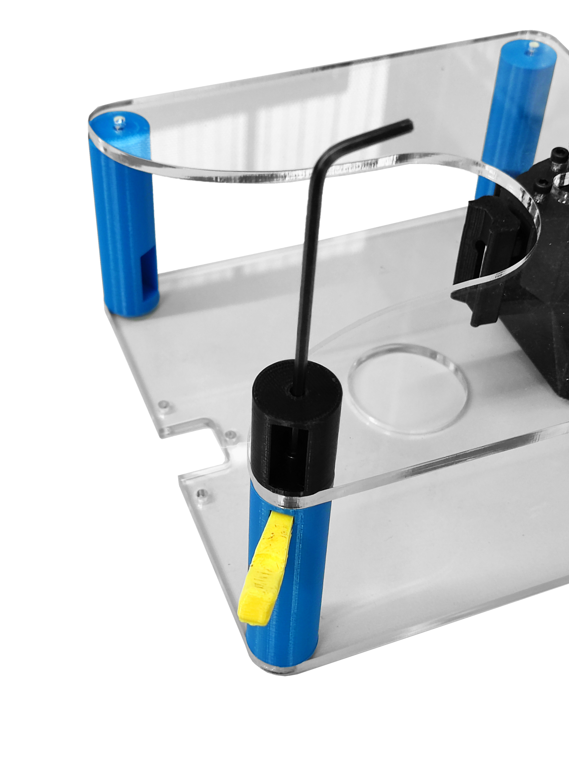
images/standoff-M-attached.jpg
