wenzel-lab/flow-microscopy-platform/images/standoff-M-nut.jpg

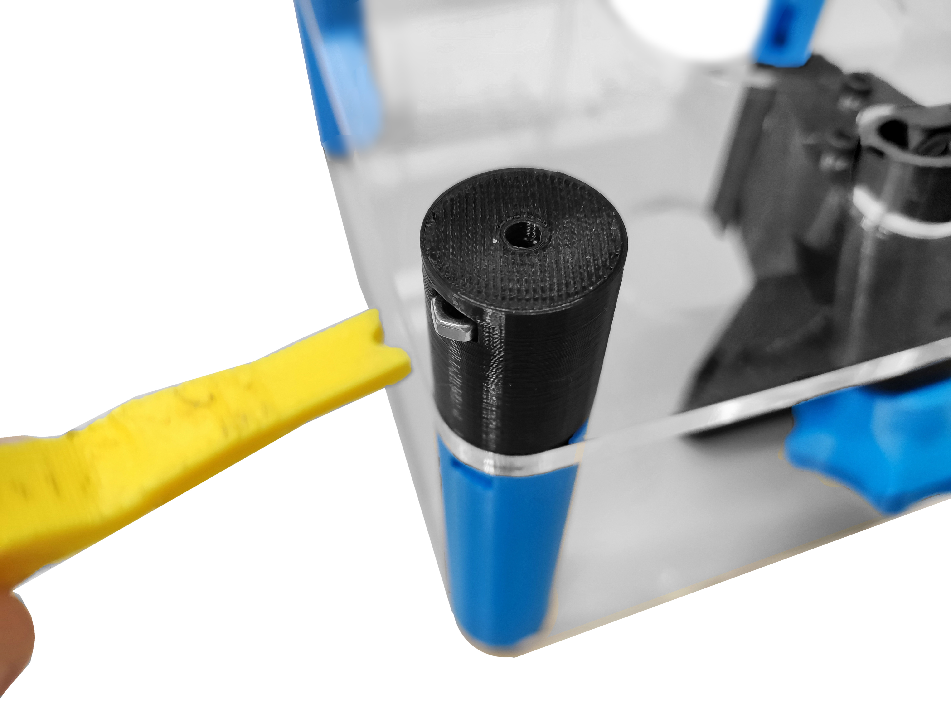
images/standoff-M-nut.jpg
