wenzel-lab/flow-microscopy-platform/images/standoff-M-nut_1.jpg

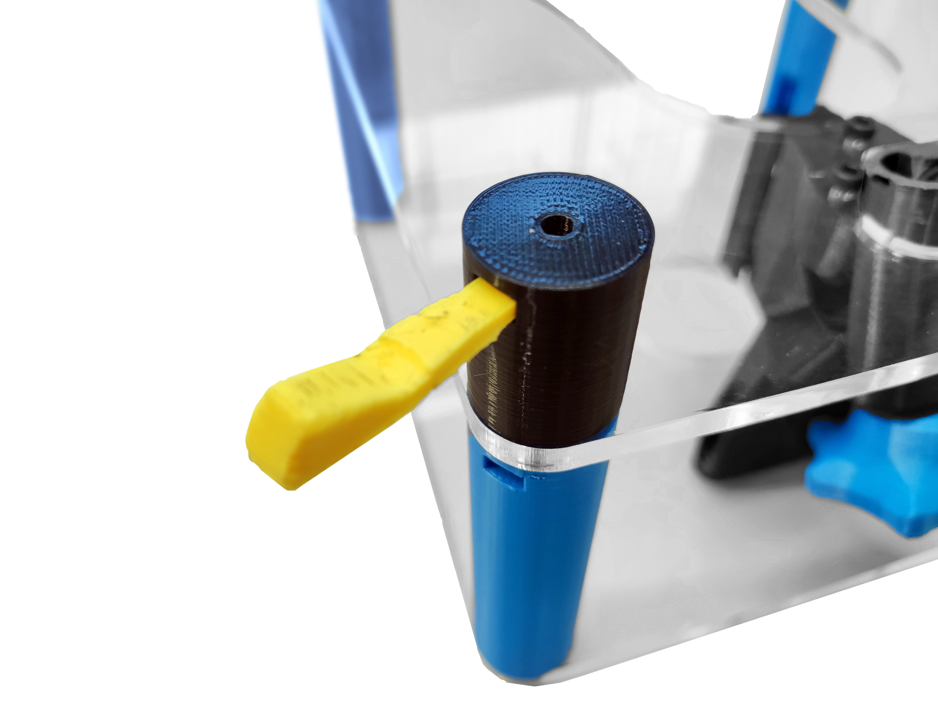
images/standoff-M-nut_1.jpg
