wenzel-lab/flow-microscopy-platform/images/standoff-M.jpg

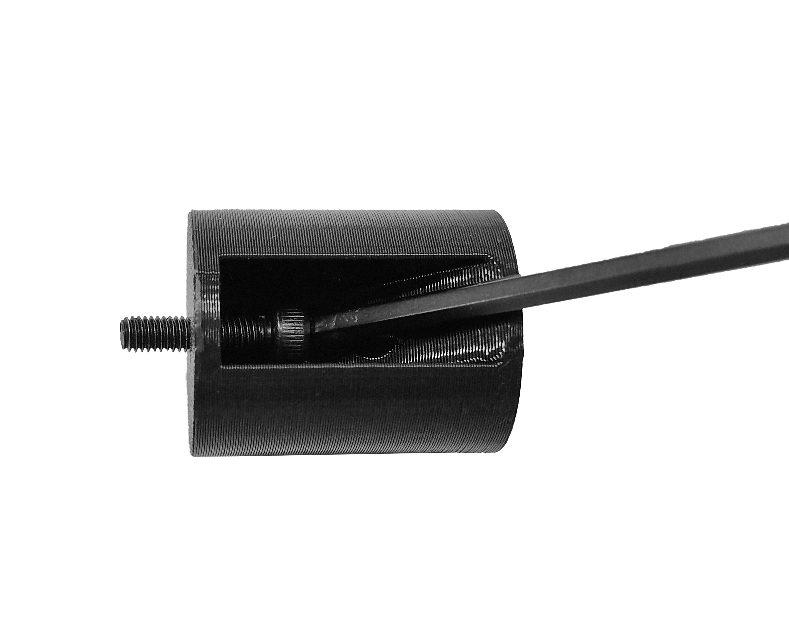
images/standoff-M.jpg
