wenzel-lab/flow-microscopy-platform/images/standoff-screw.jpg

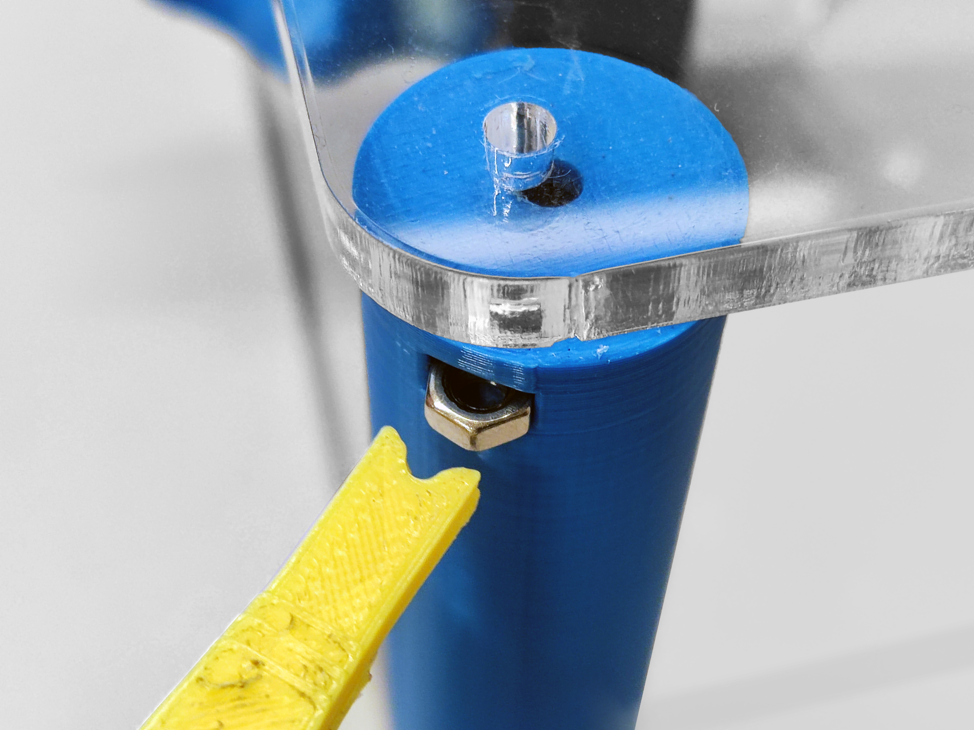
images/standoff-screw.jpg
