wenzel-lab/flow-microscopy-platform/images/standoff-screw_1.jpg

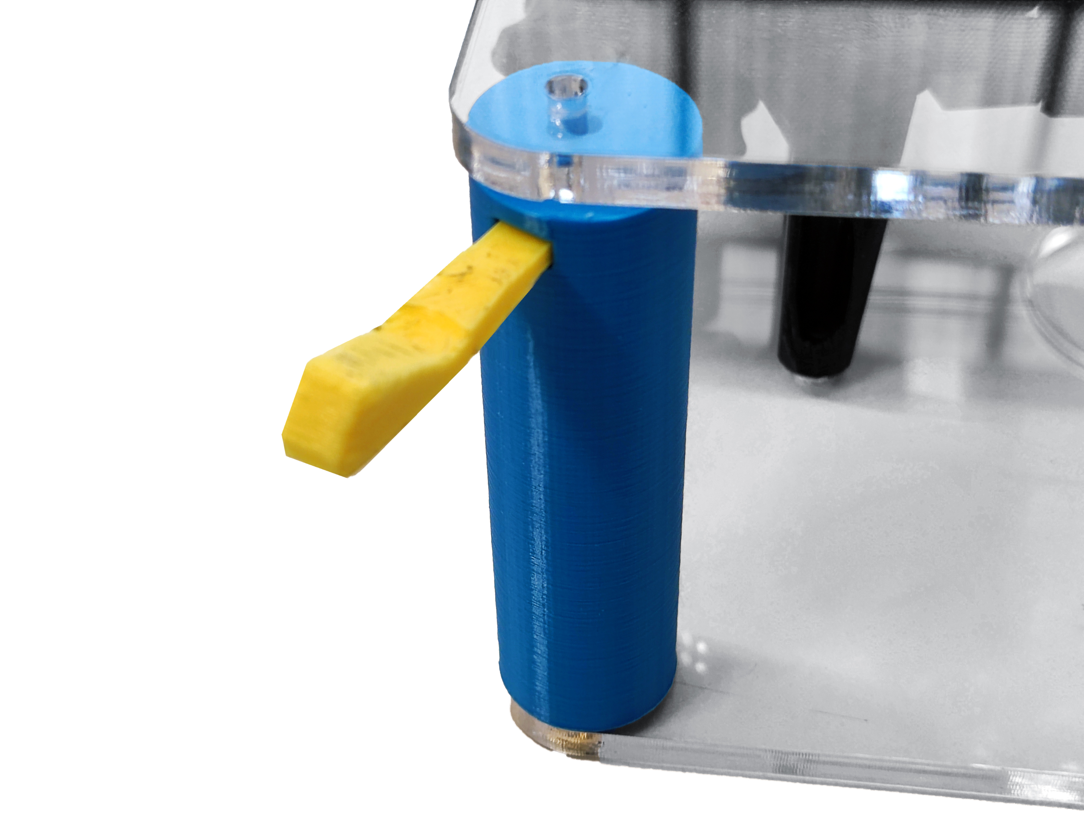
images/standoff-screw_1.jpg
