wenzel-lab/flow-microscopy-platform/images/tap_bottom_plate.jpg

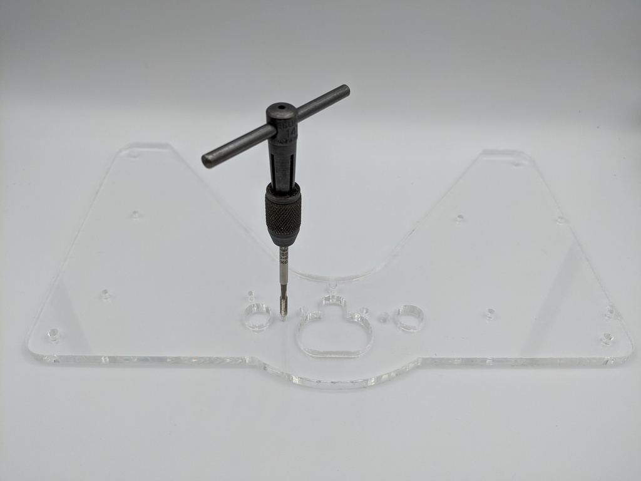
images/tap_bottom_plate.jpg
