wenzel-lab/flow-microscopy-platform/images/tap_top_plate_1.jpg

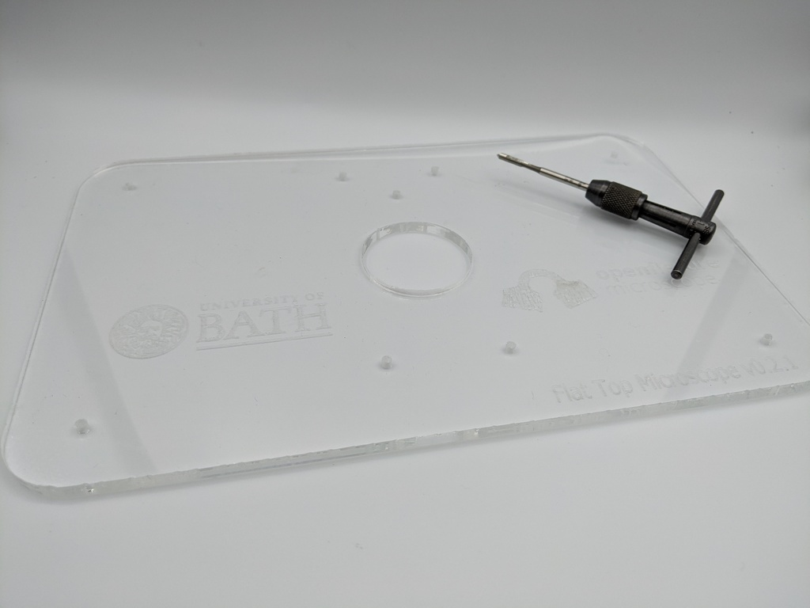
images/tap_top_plate_1.jpg
