wenzel-lab/flow-microscopy-platform/images/tap_top_plate_2.jpg

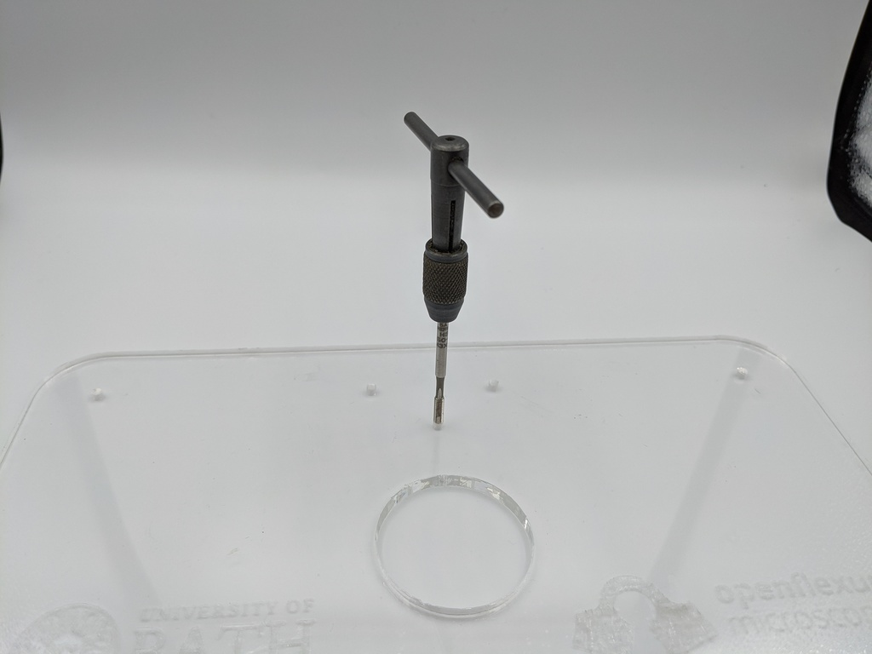
images/tap_top_plate_2.jpg
