wenzel-lab/flow-microscopy-platform/images/threelevelss.jpg

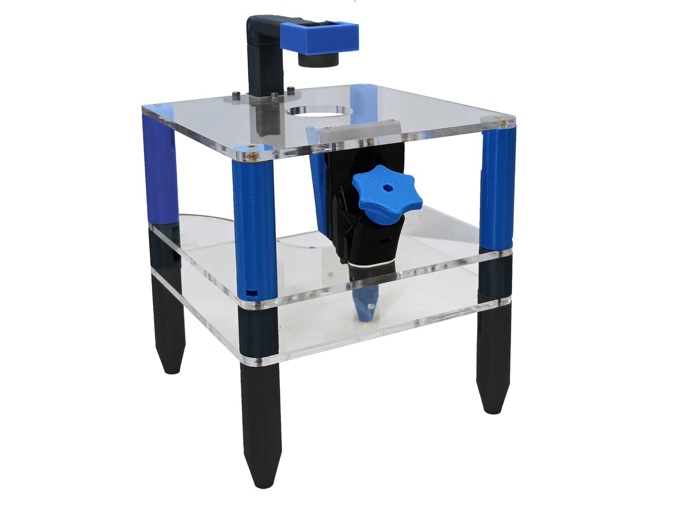
images/threelevelss.jpg
