wenzel-lab/flow-microscopy-platform/images/thumbscrew-slider.png

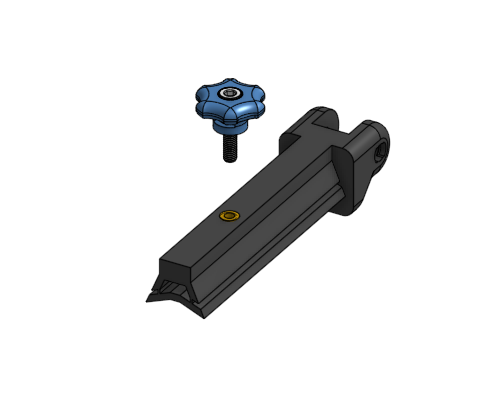
images/thumbscrew-slider.png
