wenzel-lab/flow-microscopy-platform/images/thumbscrew-slider_1.png

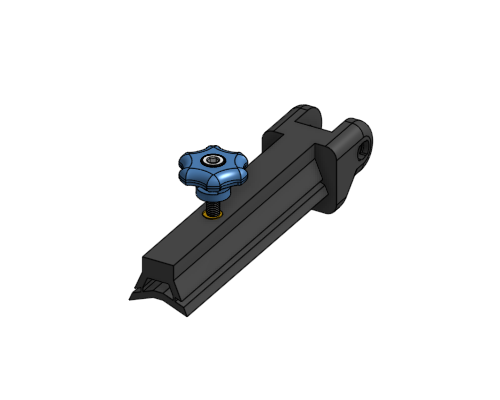
images/thumbscrew-slider_1.png
