wenzel-lab/flow-microscopy-platform/images/thumbscrew.png

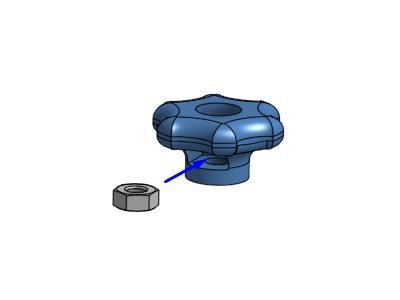
images/thumbscrew.png
