wenzel-lab/flow-microscopy-platform/images/thumbscrew_2.png

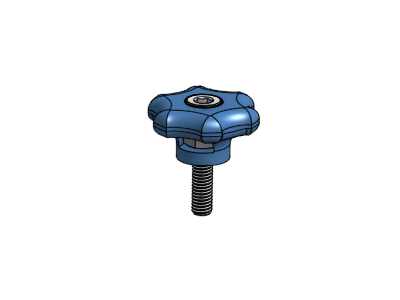
images/thumbscrew_2.png
