wenzel-lab/flow-microscopy-platform/parts/mech/M6-16i.md

---
PartData:
    Specs:
        Type: M6
        Length: 16mm
        Material: Stainless steel
        Tool needed: HEX key
        Supplier:  -[Aliexpress](aliexpress.com/item/1005008731102942.html)
---

# M6 x 16 inner screw

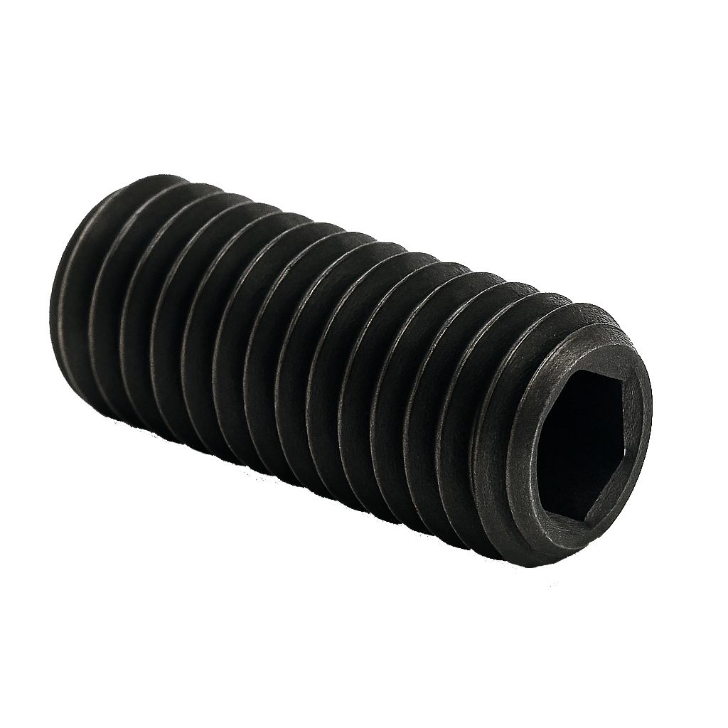
[picture p158: images/InnerScrew.png]
