wenzel-lab/flow-microscopy-platform/parts/mech/nuts.md

# Nut

Small hexagonal or square-shaped object with a threaded hole used to fasten objects together. It pairs with a screw.

*Supplier:* [Aliexpress](https://es.aliexpress.com/item/1005009117772752.html)
