wenzel-lab/flow-microscopy-platform/parts/mech/washer.md

---
PartData:
    Specs:
        Type: M3
        Material: Stainless steel
        Supplier:  -[Aliexpress](aliexpress.com/item/1005008724152831.html)

---
# Screw washer

* Small disk used with screws or bolts. It distributes the load and protects surfaces. It prevents damage and provides stability. Different materials and types are available for specific applications. It enhances the performance of the fastening system.

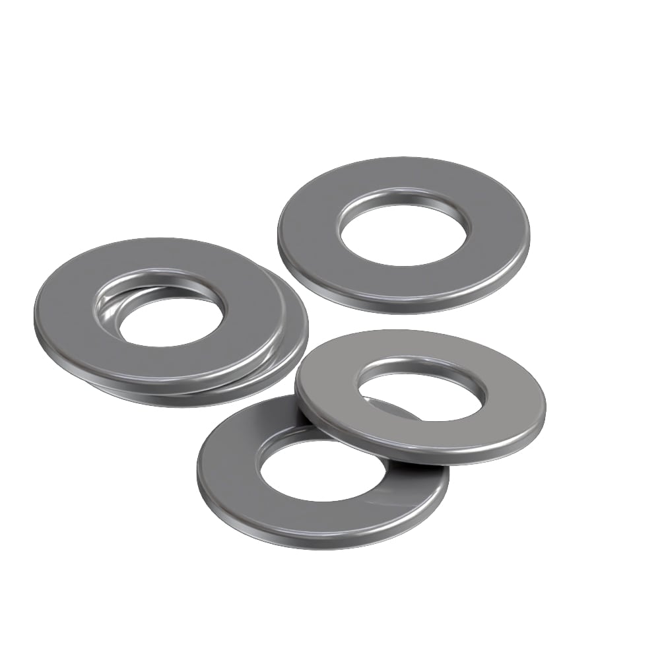
[picture p159: images/screwwasher.jpg]
