wenzel-lab/flow-microscopy-platform/parts/mech/X-M3-20.md

---
PartData:
    Specs:
        Type: M3
        Length: 20 mm
        Material: Stainless steel
        Tool needed: screwdriver
        Supplier:  -[Pernos kim](https://pernos-kim.negocio.site/)
---
# M3 X Screw

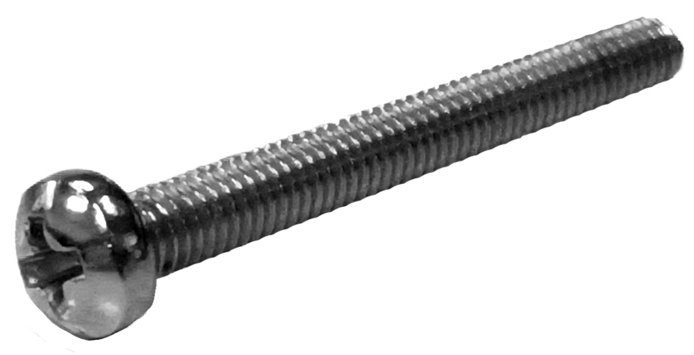
[picture p160: images/screw.jpg]
