wenzel-lab/flow-microscopy-platform/parts/tools/1.5mmBallEndAllenKey.md

# 1.5 mm Ball-end Allen Key

Tool used to drive screws or bolts with hexagonal sockets. It has a metal shaft with a hexagonal cross-section. They come in different sizes for various applications.

It is important that the Allen key has a ball end:

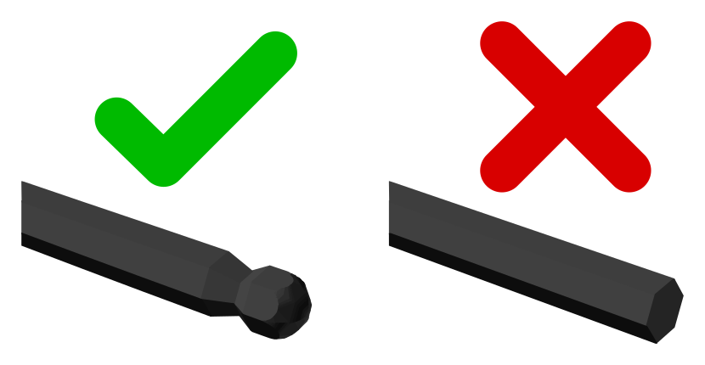
[picture p161: parts/tools/diagram/AllenKeyBall.png]
