wenzel-lab/flow-microscopy-platform/parts/tools/laser-cutting-machine.md

# Laser cutting machine 

High-precision tool that uses a focused laser beam to cut through or engrave various materials.

It offers versatility in cutting intricate shapes, patterns, and designs in materials like wood, acrylic, metal and fabric.

Laser cutting machines are used in industries like manufacturing, crafting, signage, and engineering for precise and efficient material processing.
