wenzel-lab/flow-microscopy-platform/parts/tools/pi_camera_lens_tool.md

# Pi camera lens tool

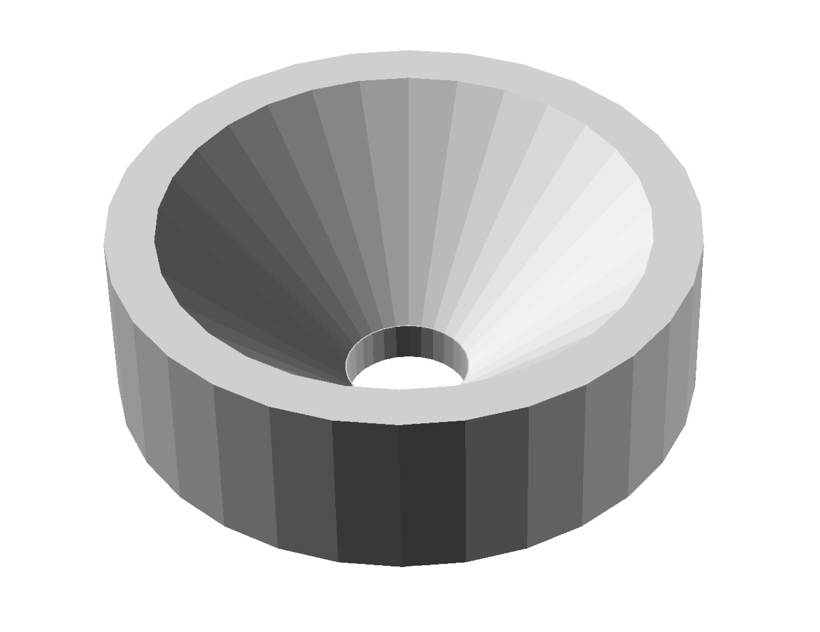
[picture p162: images/picamlt.jpg]
