wenzel-lab/flow-microscopy-platform/parts/tools/screwdriver.md

# Screwdriver

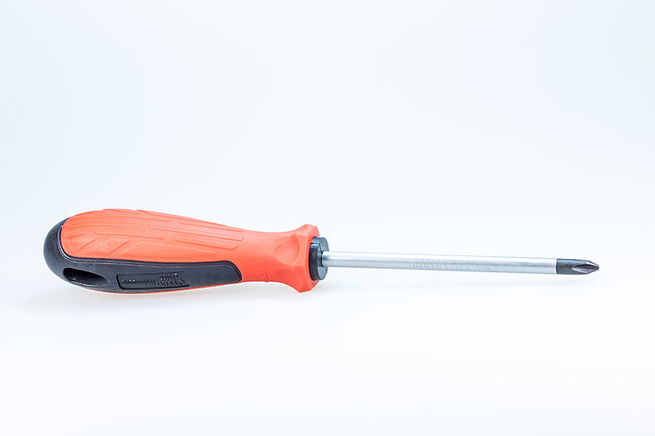
[picture p164: images/screwdriver.jpg]
