wenzel-lab/flow-microscopy-platform/parts/mech/oring.md

# O ring

Elastic ring made of viton with a 34x3 mm. diameter.

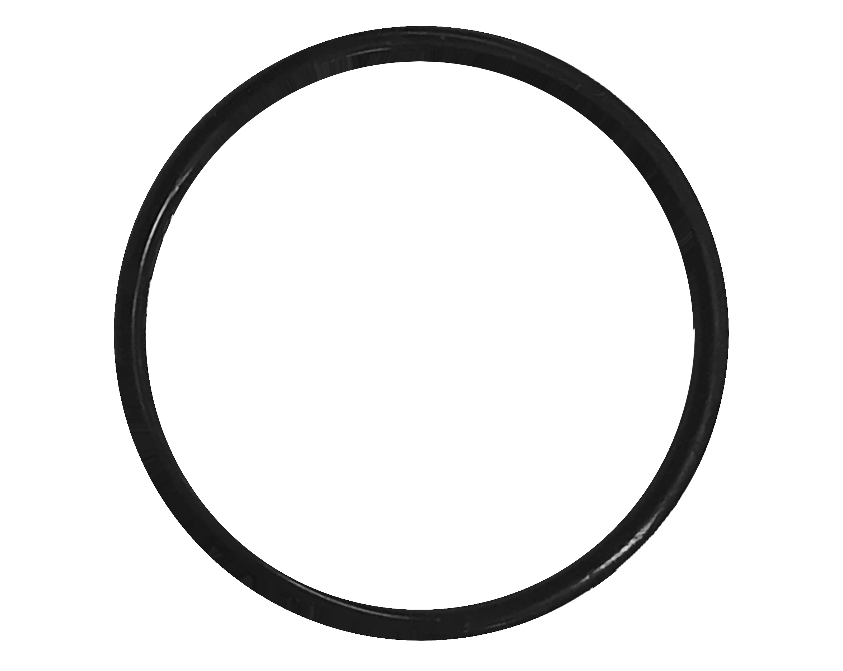
[picture p168: images/oring.jpg]


_Supplier:_ [o-ring stocks](https://www.o-ring-stocks.com)
