wenzel-lab/flow-microscopy-platform/parts/tools/crimper.md

# Crimper

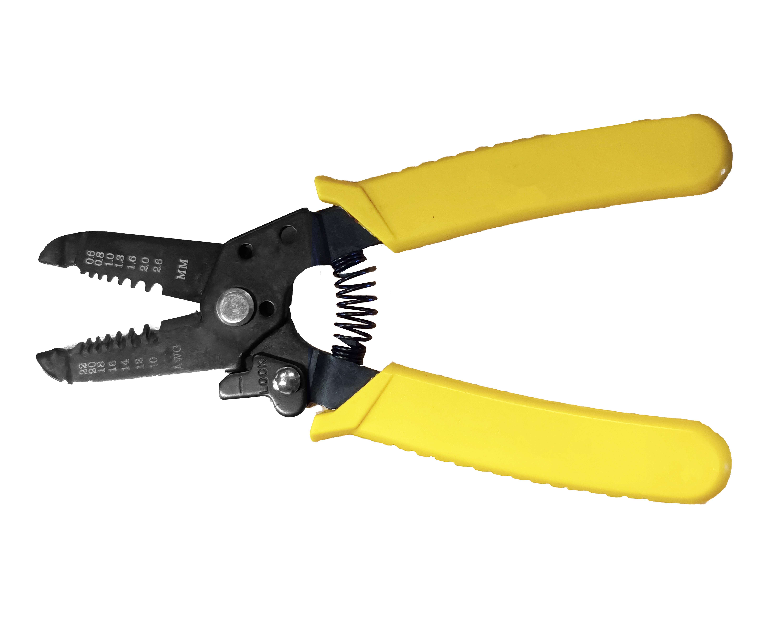
[picture p169: images/Crimper.jpg]
