wenzel-lab/flow-microscopy-platform/parts/tools/pliers.md

# Needle-nose plier

Hand tool with long, slender jaws that taper to a fine point.
Used for gripping and manipulating small objects in tight or hard-to-reach spaces.

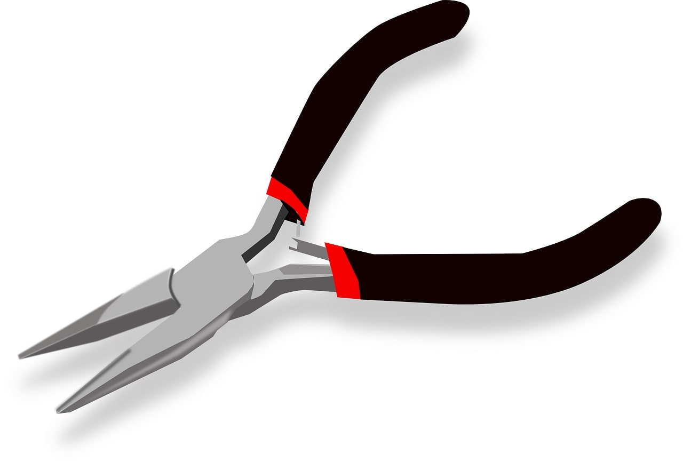
[picture p170: images/pliersLCC.jpg]
