wenzel-lab/flow-microscopy-platform/parts/tools/tweezers.md

# Tweezers

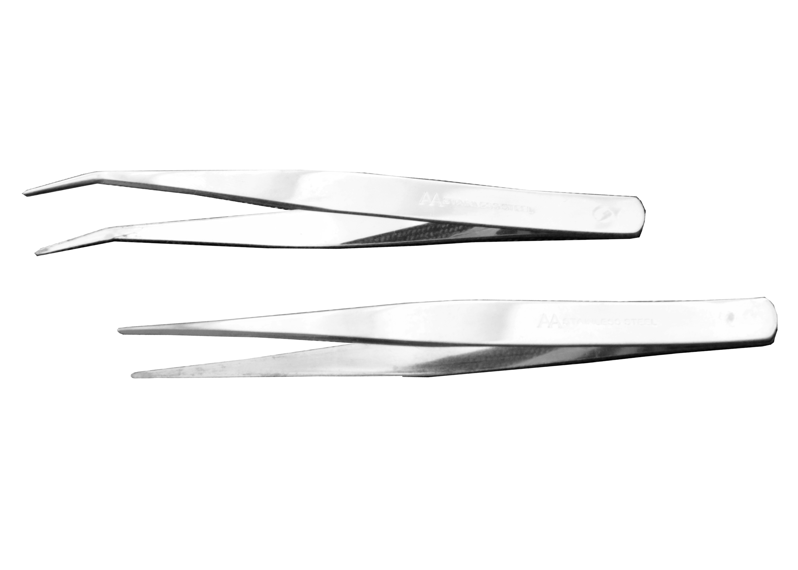
[picture p171: images/Tweezers.jpg]


Small, handheld tools with two arms and pointed tips, used for picking up and manipulating small objects with precision.
