wenzel-lab/flow-microscopy-platform/models/Holders-middle-plate.stl

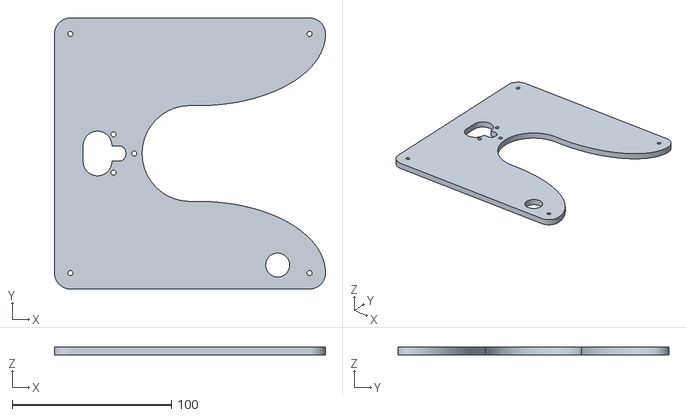
[picture p186: CAD file, 2026-01-13]
models/Holders-middle-plate.stl
170.0 x 170.0 x 5.00
