wenzel-lab/flow-microscopy-platform/models/top-plate.stl

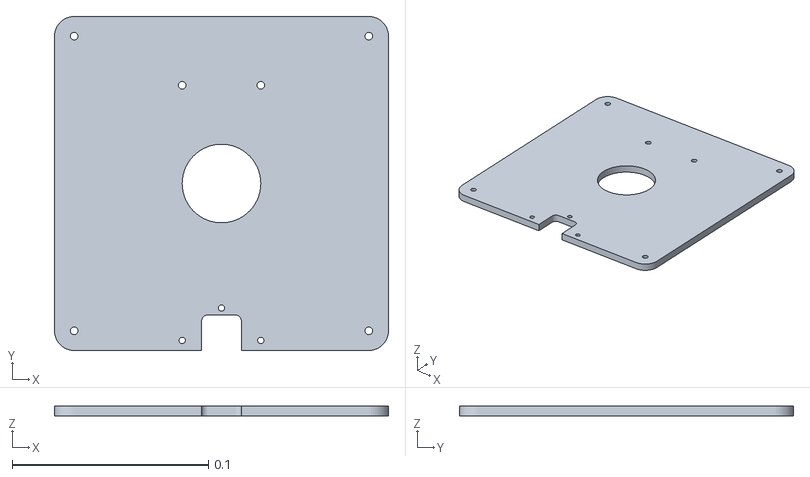
[picture p187: CAD file, 2026-01-13]
models/top-plate.stl
0.17 x 0.17 x 0.005
