wenzel-lab/flow-microscopy-platform/models/leg_test.stl

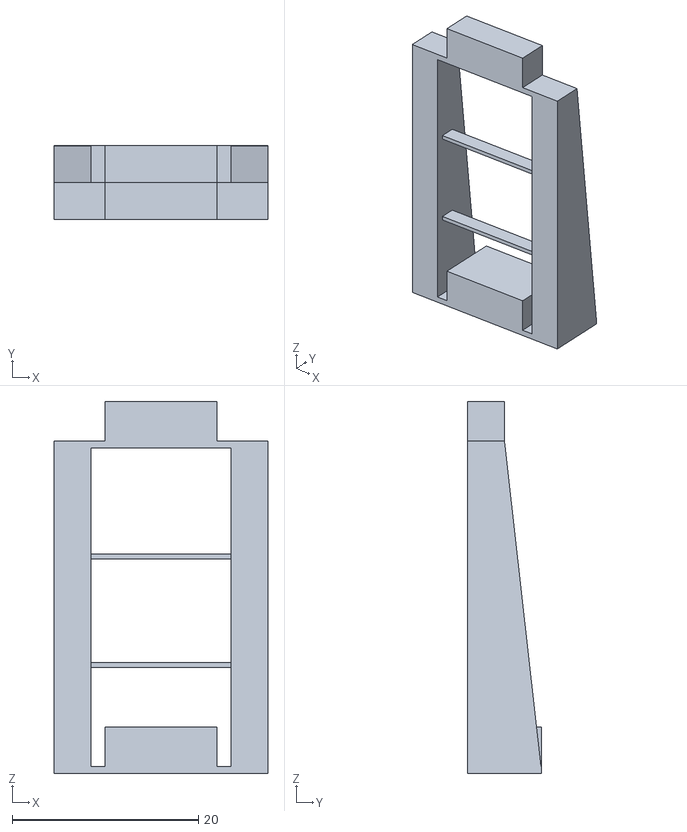
[picture p188: CAD file, 2026-01-13]
models/leg_test.stl
23.0 x 8.00 x 40.0
