wenzel-lab/flow-microscopy-platform/models/illumination-base.stl

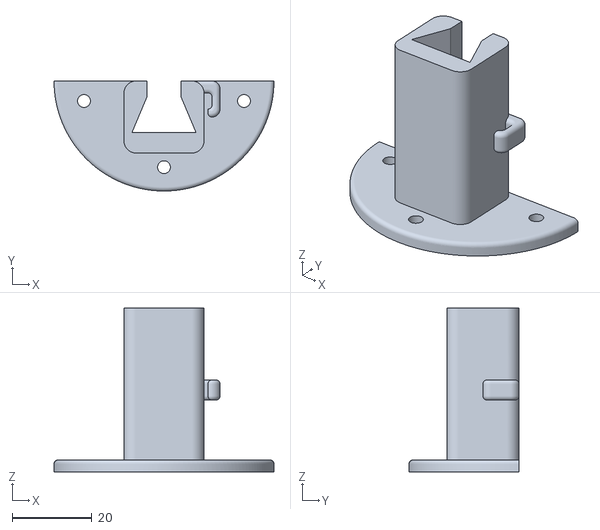
[picture p189: CAD file, 2026-01-13]
models/illumination-base.stl
55.0 x 27.5 x 41.0
