wenzel-lab/flow-microscopy-platform/models/illumination-slider.stl

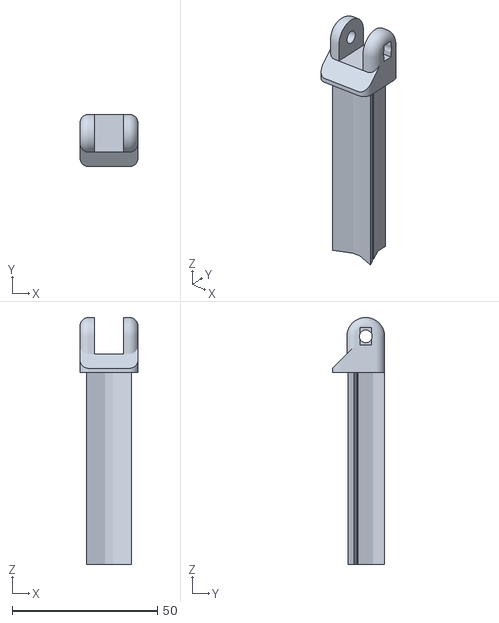
[picture p190: CAD file, 2026-01-13]
models/illumination-slider.stl
20.0 x 18.0 x 85.0
