wenzel-lab/flow-microscopy-platform/models/camera-platform.stl

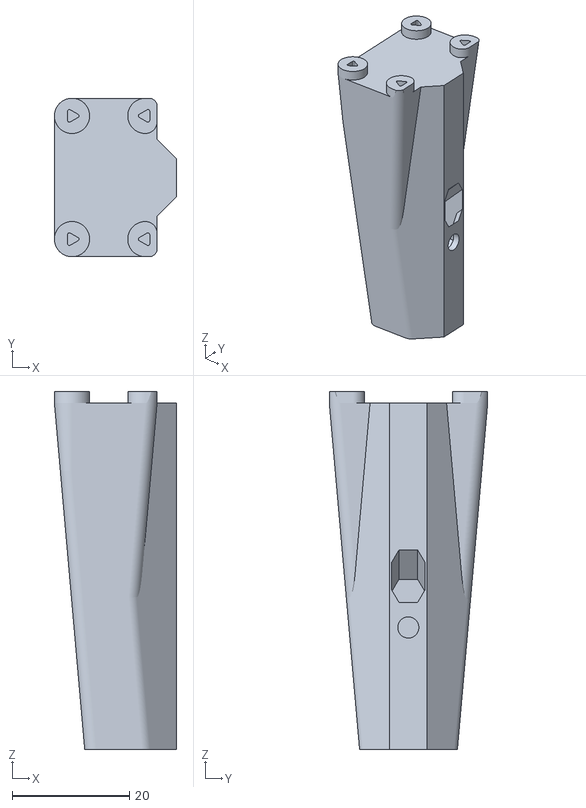
[picture p191: CAD file, 2026-01-13]
models/camera-platform.stl
20.8 x 27.0 x 61.0
