wenzel-lab/flow-microscopy-platform/models/Holders-top-plate.stl

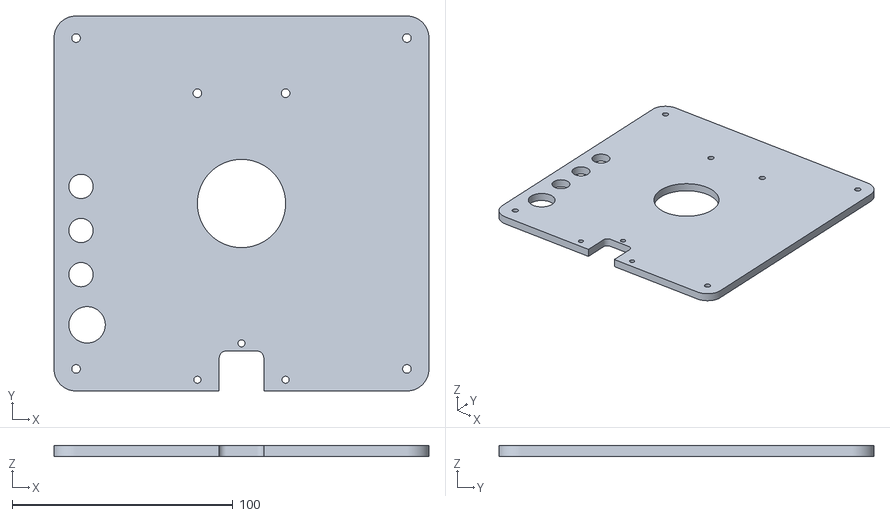
[picture p192: CAD file, 2026-01-13]
models/Holders-top-plate.stl
170.0 x 170.0 x 5.00
