wenzel-lab/flow-microscopy-platform/models/led-cover.stl

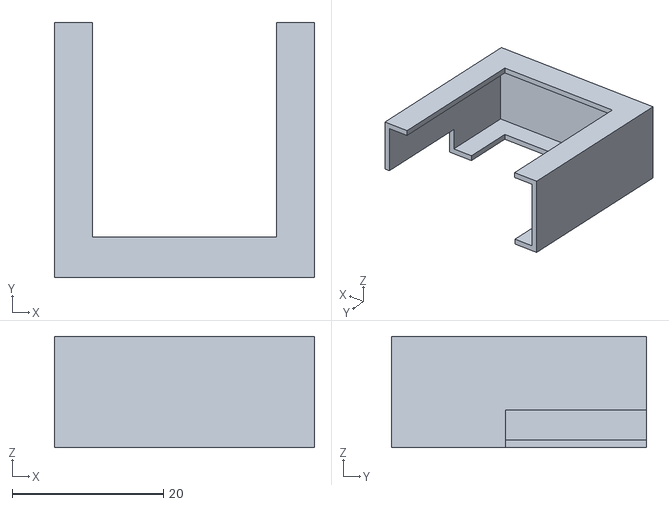
[picture p193: CAD file, 2026-01-13]
models/led-cover.stl
34.4 x 33.8 x 14.7
