wenzel-lab/flow-microscopy-platform/models/foot-M.stl

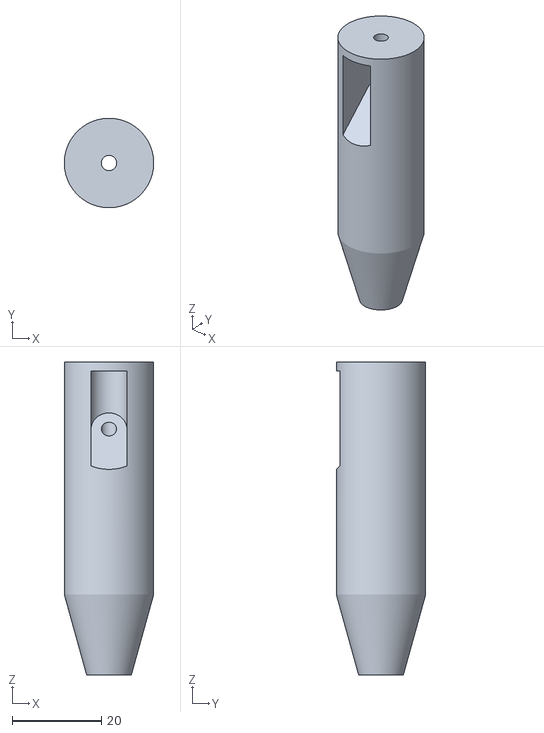
[picture p194: CAD file, 2026-01-13]
models/foot-M.stl
20.0 x 20.0 x 70.0
