wenzel-lab/flow-microscopy-platform/models/led-arm.stl

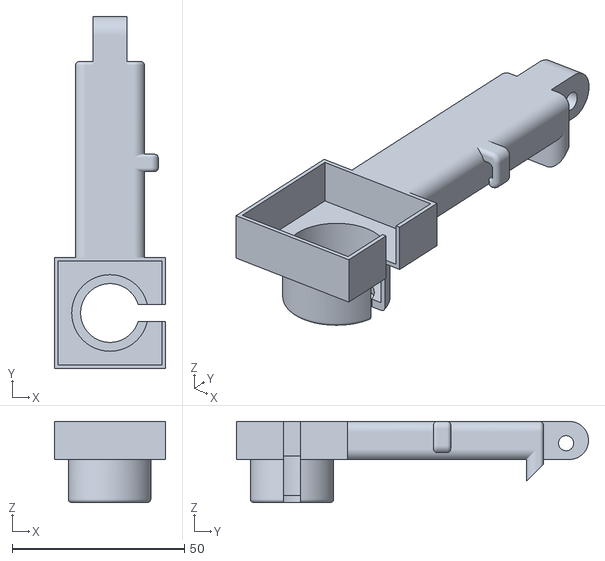
[picture p195: CAD file, 2026-01-13]
models/led-arm.stl
32.2 x 102.1 x 23.5
