wenzel-lab/flow-microscopy-platform/models/lens-spacer.stl

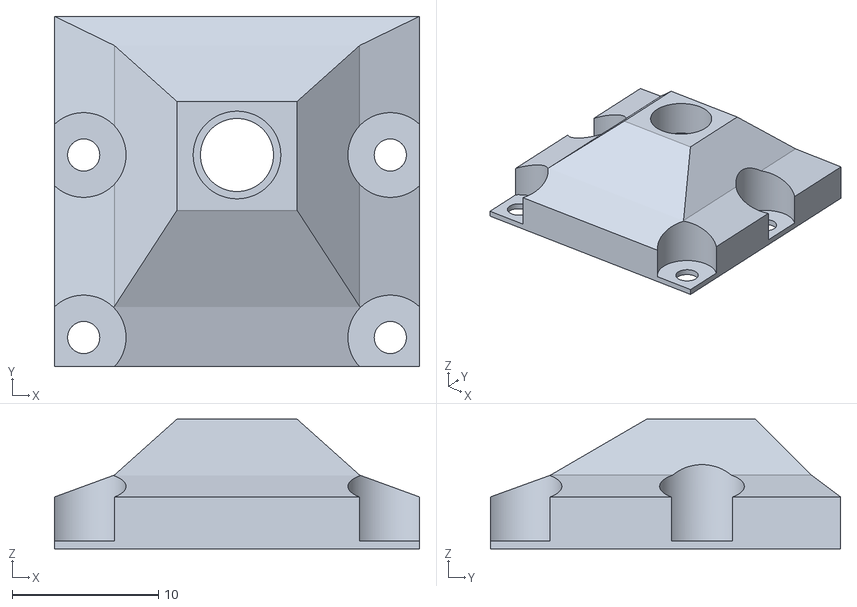
[picture p196: CAD file, 2026-01-13]
models/lens-spacer.stl
25.0 x 24.0 x 8.88
