wenzel-lab/flow-microscopy-platform/models/standoff-M.stl

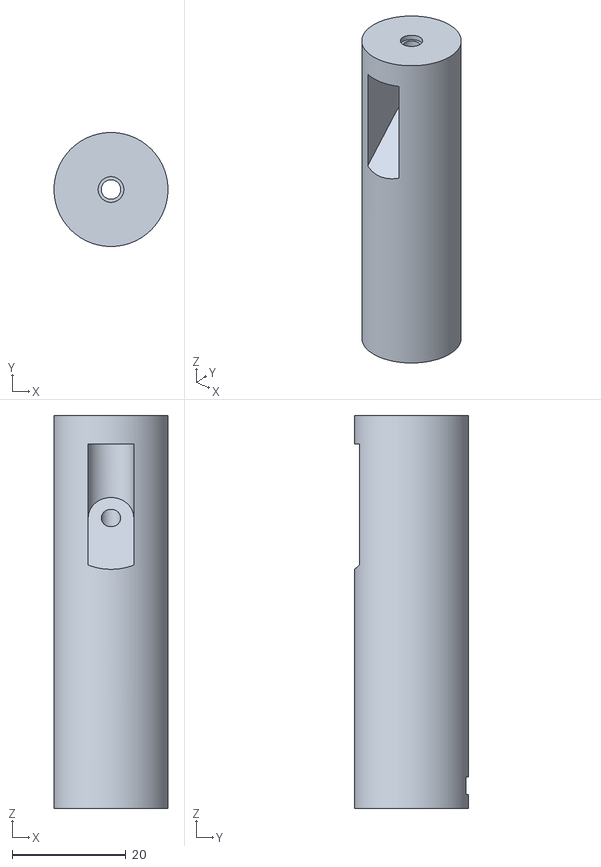
[picture p197: CAD file, 2026-01-13]
models/standoff-M.stl
20.0 x 20.0 x 69.0
