wenzel-lab/flow-microscopy-platform/models/screencase.stl

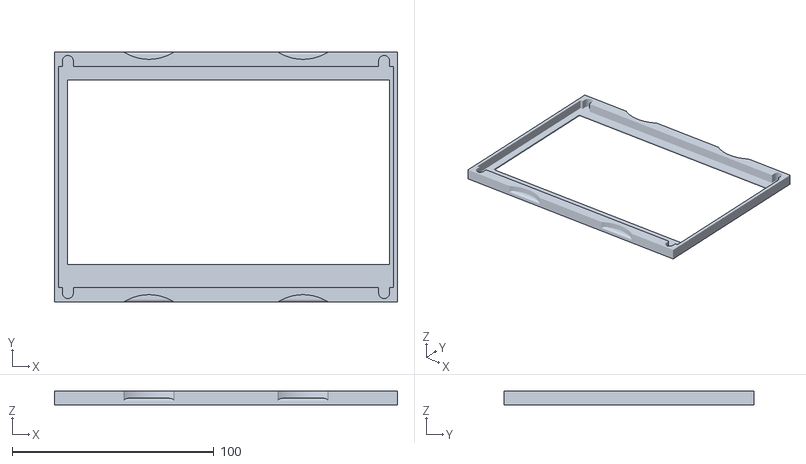
[picture p198: CAD file, 2026-01-13]
models/screencase.stl
170.1 x 124.0 x 6.80
