wenzel-lab/flow-microscopy-platform/models/spacer-4mm.stl

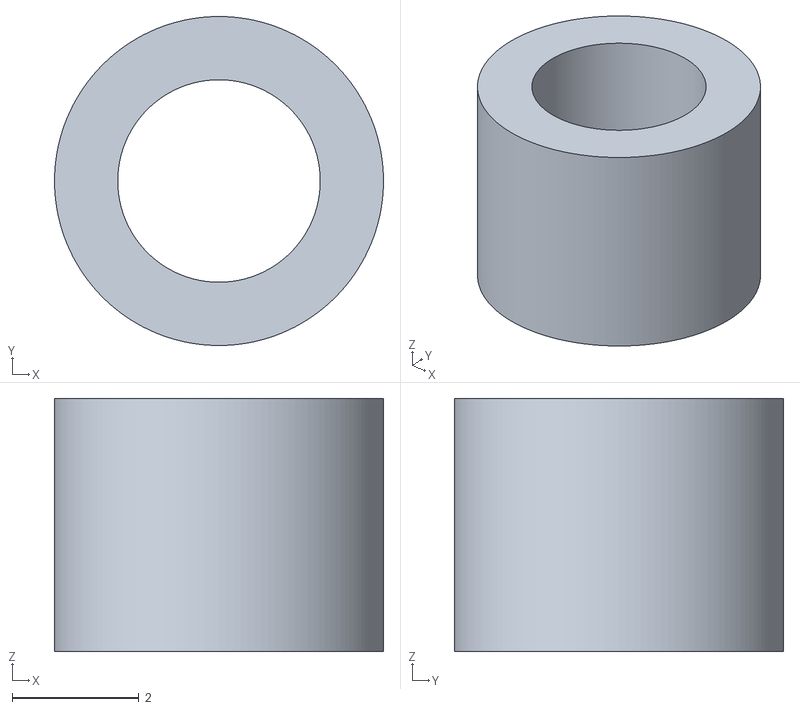
[picture p199: CAD file, 2026-01-13]
models/spacer-4mm.stl
5.20 x 5.20 x 4.00
