wenzel-lab/flow-microscopy-platform/models/spacer-11mm.stl

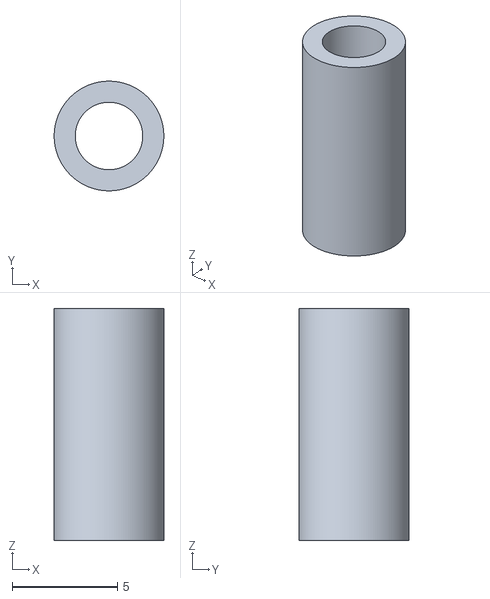
[picture p200: CAD file, 2026-01-13]
models/spacer-11mm.stl
5.20 x 5.20 x 11.0
