wenzel-lab/flow-microscopy-platform/images/focus_assembly_top_attached.jpg

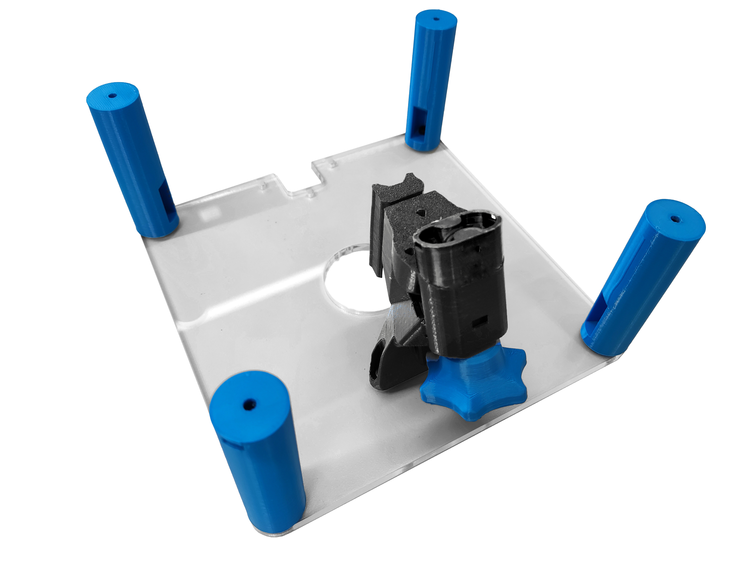
images/focus_assembly_top_attached.jpg
