wenzel-lab/flow-microscopy-platform/images/focus_assembly_top_attached_1.jpg

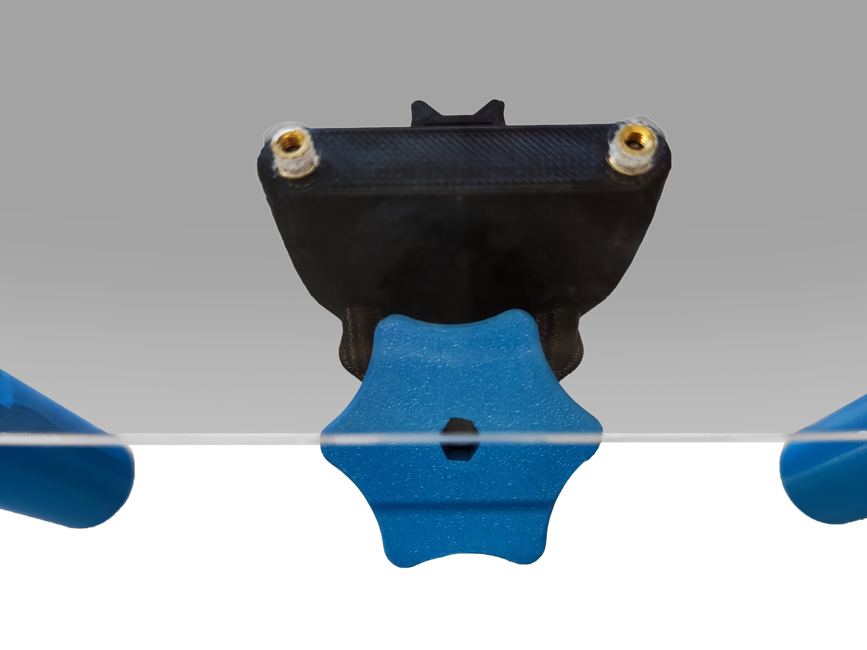
images/focus_assembly_top_attached_1.jpg
