wenzel-lab/flow-microscopy-platform/images/focus_assembly_top_attachment.jpg

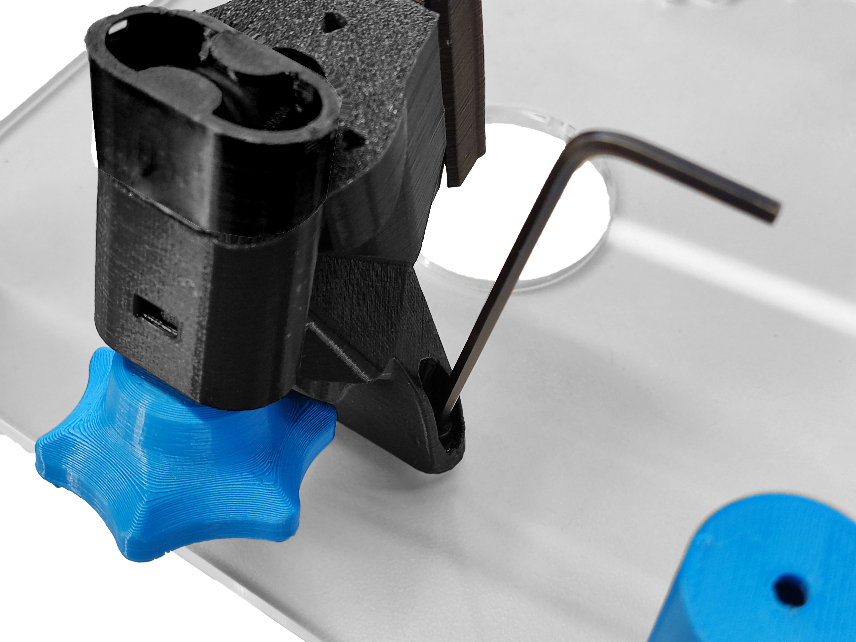
images/focus_assembly_top_attachment.jpg
