wenzel-lab/flow-microscopy-platform/images/led-assembly-arm.png

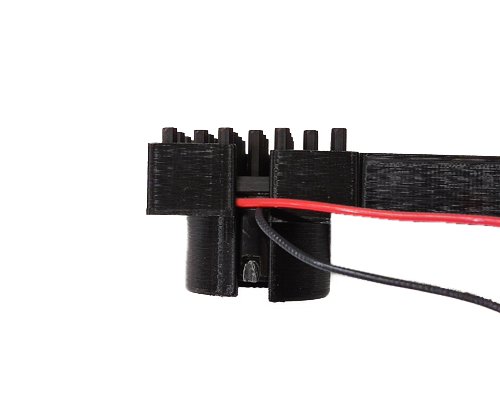
images/led-assembly-arm.png
