wenzel-lab/flow-microscopy-platform/images/led-assembly-arm_1.jpg

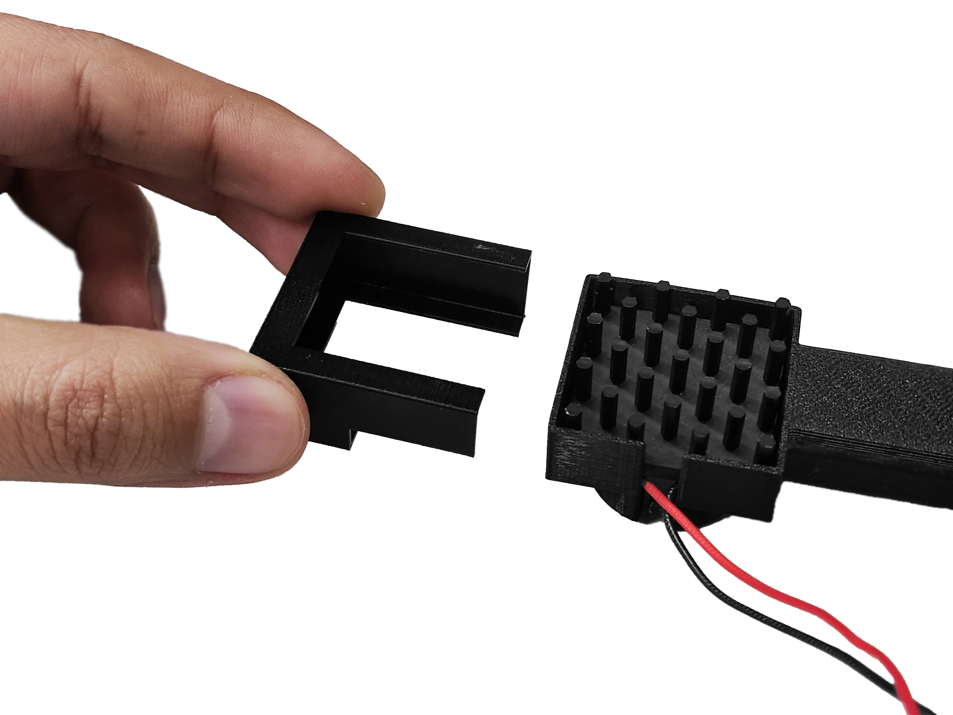
images/led-assembly-arm_1.jpg
