wenzel-lab/flow-microscopy-platform/images/led-assembly-arm_3.jpg

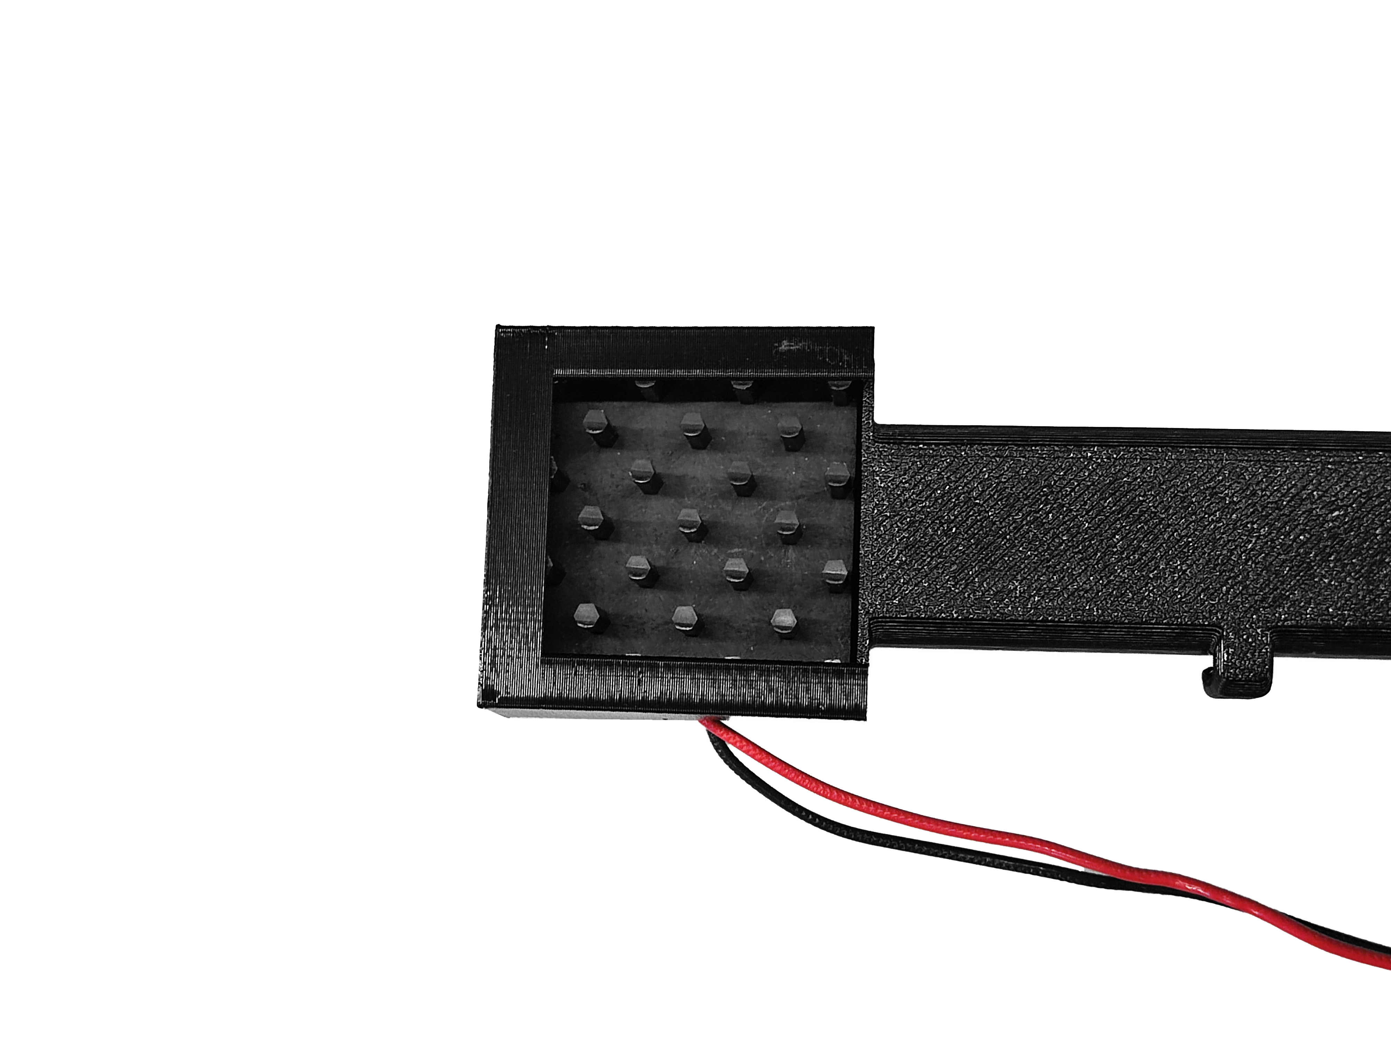
images/led-assembly-arm_3.jpg
