wenzel-lab/flow-microscopy-platform/images/low_cost_optics_assembly_camera.png

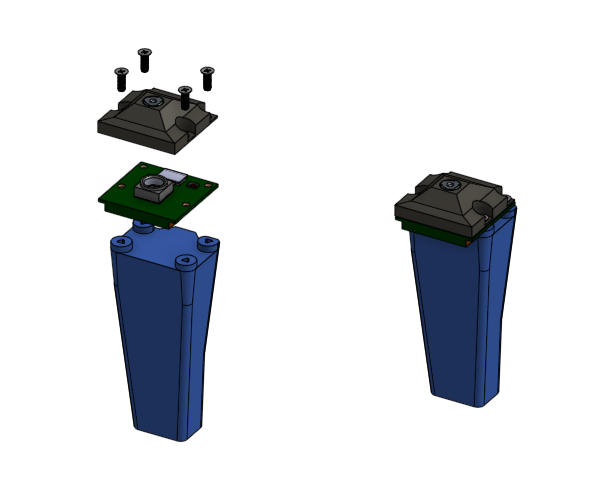
images/low_cost_optics_assembly_camera.png
