wenzel-lab/flow-microscopy-platform/images/low_cost_optics_assembly_ribbon.jpg

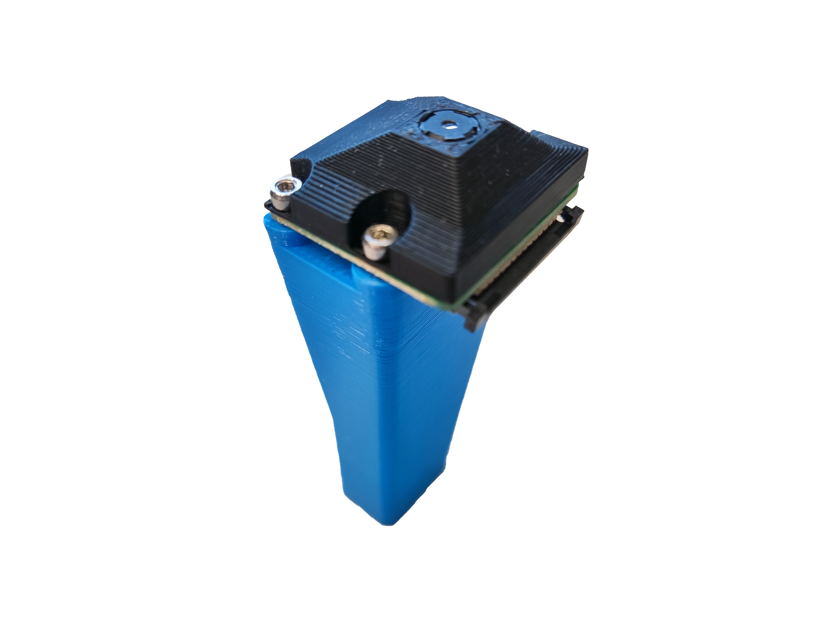
images/low_cost_optics_assembly_ribbon.jpg
