wenzel-lab/flow-microscopy-platform/images/test-matrix-1.jpg

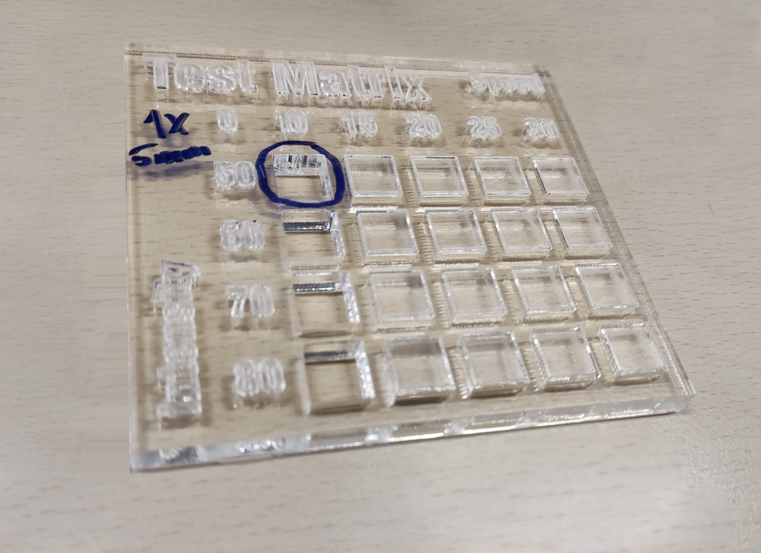
images/test-matrix-1.jpg
